peterloes/HRD/Software/Device/EnergyMicro/EFM32G/Include/efm32g200f16.h

/**************************************************************************//**
 * @file
 * @brief CMSIS Cortex-M3 Peripheral Access Layer Header File
 *        for EFM EFM32G200F16
 * @author Energy Micro AS
 * @version 3.20.2
 ******************************************************************************
 * @section License
 * <b>(C) Copyright 2012 Energy Micro AS, http://www.energymicro.com</b>
 ******************************************************************************
 *
 * Permission is granted to anyone to use this software for any purpose,
 * including commercial applications, and to alter it and redistribute it
 * freely, subject to the following restrictions:
 *
 * 1. The origin of this software must not be misrepresented; you must not
 *    claim that you wrote the original software.
 * 2. Altered source versions must be plainly marked as such, and must not be
 *    misrepresented as being the original software.
 * 3. This notice may not be removed or altered from any source distribution.
 *
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
 * Energy Micro AS will not be liable for any consequential, incidental, or
 * special damages, or any other relief, or for any claim by any third party,
 * arising from your use of this Software.
 *
 *****************************************************************************/

#ifndef __EFM32G200F16_H
#define __EFM32G200F16_H

#ifdef __cplusplus
extern "C" {
#endif

/**************************************************************************//**
 * @addtogroup Parts
 * @{
 *****************************************************************************/

/**************************************************************************//**
 * @defgroup EFM32G200F16 EFM32G200F16
 * @{
 *****************************************************************************/

/** Interrupt Number Definition */
typedef enum IRQn
{
/******  Cortex-M3 Processor Exceptions Numbers *******************************************/
  NonMaskableInt_IRQn   = -14,              /*!< 2 Non Maskable Interrupt                 */
  HardFault_IRQn        = -13,              /*!< 3 Cortex-M3 Hard Fault Interrupt         */
  MemoryManagement_IRQn = -12,              /*!< 4 Cortex-M3 Memory Management Interrupt  */
  BusFault_IRQn         = -11,              /*!< 5 Cortex-M3 Bus Fault Interrupt          */
  UsageFault_IRQn       = -10,              /*!< 6 Cortex-M3 Usage Fault Interrupt        */
  SVCall_IRQn           = -5,               /*!< 11 Cortex-M3 SV Call Interrupt           */
  DebugMonitor_IRQn     = -4,               /*!< 12 Cortex-M3 Debug Monitor Interrupt     */
  PendSV_IRQn           = -2,               /*!< 14 Cortex-M3 Pend SV Interrupt           */
  SysTick_IRQn          = -1,               /*!< 15 Cortex-M3 System Tick Interrupt       */

/******  EFM32G Peripheral Interrupt Numbers **********************************************/
  DMA_IRQn              = 0,  /*!< 16+0 EFM32 DMA Interrupt */
  GPIO_EVEN_IRQn        = 1,  /*!< 16+1 EFM32 GPIO_EVEN Interrupt */
  TIMER0_IRQn           = 2,  /*!< 16+2 EFM32 TIMER0 Interrupt */
  USART0_RX_IRQn        = 3,  /*!< 16+3 EFM32 USART0_RX Interrupt */
  USART0_TX_IRQn        = 4,  /*!< 16+4 EFM32 USART0_TX Interrupt */
  ACMP0_IRQn            = 5,  /*!< 16+5 EFM32 ACMP0 Interrupt */
  ADC0_IRQn             = 6,  /*!< 16+6 EFM32 ADC0 Interrupt */
  DAC0_IRQn             = 7,  /*!< 16+7 EFM32 DAC0 Interrupt */
  I2C0_IRQn             = 8,  /*!< 16+8 EFM32 I2C0 Interrupt */
  GPIO_ODD_IRQn         = 9,  /*!< 16+9 EFM32 GPIO_ODD Interrupt */
  TIMER1_IRQn           = 10, /*!< 16+10 EFM32 TIMER1 Interrupt */
  USART1_RX_IRQn        = 12, /*!< 16+12 EFM32 USART1_RX Interrupt */
  USART1_TX_IRQn        = 13, /*!< 16+13 EFM32 USART1_TX Interrupt */
  LEUART0_IRQn          = 18, /*!< 16+18 EFM32 LEUART0 Interrupt */
  LETIMER0_IRQn         = 20, /*!< 16+20 EFM32 LETIMER0 Interrupt */
  PCNT0_IRQn            = 21, /*!< 16+21 EFM32 PCNT0 Interrupt */
  RTC_IRQn              = 24, /*!< 16+24 EFM32 RTC Interrupt */
  CMU_IRQn              = 25, /*!< 16+25 EFM32 CMU Interrupt */
  VCMP_IRQn             = 26, /*!< 16+26 EFM32 VCMP Interrupt */
  MSC_IRQn              = 28, /*!< 16+28 EFM32 MSC Interrupt */
} IRQn_Type;

/**************************************************************************//**
 * @defgroup EFM32G200F16_Core EFM32G200F16 Core
 * @{
 * @brief Processor and Core Peripheral Section
 *****************************************************************************/
#define __MPU_PRESENT             1 /**< Presence of MPU  */
#define __NVIC_PRIO_BITS          3 /**< NVIC interrupt priority bits */
#define __Vendor_SysTickConfig    0 /**< Is 1 if different SysTick counter is used */

/** @} End of group EFM32G200F16_Core */

/**************************************************************************//**
* @defgroup EFM32G200F16_Part EFM32G200F16 Part
* @{
******************************************************************************/

/** Part family */
#define _EFM32_GECKO_FAMILY    1 /**< Gecko EFM32G MCU Family */
#define _EFM_DEVICE              /**< Energy Micro EFM-type microcontroller */

/* If part number is not defined as compiler option, define it */
#if !defined(EFM32G200F16)
#define EFM32G200F16    1 /**< Gecko Part  */
#endif

/** Configure part number */
#define PART_NUMBER          "EFM32G200F16" /**< Part Number */

/** Memory Base addresses and limits */
#define FLASH_MEM_BASE       ((uint32_t) 0x0UL)        /**< FLASH base address  */
#define FLASH_MEM_SIZE       ((uint32_t) 0x10000000UL) /**< FLASH available address space  */
#define FLASH_MEM_END        ((uint32_t) 0xFFFFFFFUL)  /**< FLASH end address  */
#define FLASH_MEM_BITS       ((uint32_t) 0x28UL)       /**< FLASH used bits  */
#define AES_MEM_BASE         ((uint32_t) 0x400E0000UL) /**< AES base address  */
#define AES_MEM_SIZE         ((uint32_t) 0x400UL)      /**< AES available address space  */
#define AES_MEM_END          ((uint32_t) 0x400E03FFUL) /**< AES end address  */
#define AES_MEM_BITS         ((uint32_t) 0x10UL)       /**< AES used bits  */
#define PER_MEM_BASE         ((uint32_t) 0x40000000UL) /**< PER base address  */
#define PER_MEM_SIZE         ((uint32_t) 0xE0000UL)    /**< PER available address space  */
#define PER_MEM_END          ((uint32_t) 0x400DFFFFUL) /**< PER end address  */
#define PER_MEM_BITS         ((uint32_t) 0x20UL)       /**< PER used bits  */
#define RAM_MEM_BASE         ((uint32_t) 0x20000000UL) /**< RAM base address  */
#define RAM_MEM_SIZE         ((uint32_t) 0x8000UL)     /**< RAM available address space  */
#define RAM_MEM_END          ((uint32_t) 0x20007FFFUL) /**< RAM end address  */
#define RAM_MEM_BITS         ((uint32_t) 0x15UL)       /**< RAM used bits  */
#define RAM_CODE_MEM_BASE    ((uint32_t) 0x10000000UL) /**< RAM_CODE base address  */
#define RAM_CODE_MEM_SIZE    ((uint32_t) 0x4000UL)     /**< RAM_CODE available address space  */
#define RAM_CODE_MEM_END     ((uint32_t) 0x10003FFFUL) /**< RAM_CODE end address  */
#define RAM_CODE_MEM_BITS    ((uint32_t) 0x14UL)       /**< RAM_CODE used bits  */
#define EBI_MEM_BASE         ((uint32_t) 0x80000000UL) /**< EBI base address  */
#define EBI_MEM_SIZE         ((uint32_t) 0x10000000UL) /**< EBI available address space  */
#define EBI_MEM_END          ((uint32_t) 0x8FFFFFFFUL) /**< EBI end address  */
#define EBI_MEM_BITS         ((uint32_t) 0x28UL)       /**< EBI used bits  */

/** Bit banding area */
#define BITBAND_PER_BASE     ((uint32_t) 0x42000000UL) /**< Peripheral Address Space bit-band area */
#define BITBAND_RAM_BASE     ((uint32_t) 0x22000000UL) /**< SRAM Address Space bit-band area */

/** Flash and SRAM limits for EFM32G200F16 */
#define FLASH_BASE           (0x00000000UL) /**< Flash Base Address */
#define FLASH_SIZE           (0x00004000UL) /**< Available Flash Memory */
#define FLASH_PAGE_SIZE      512            /**< Flash Memory page size */
#define SRAM_BASE            (0x20000000UL) /**< SRAM Base Address */
#define SRAM_SIZE            (0x00002000UL) /**< Available SRAM Memory */
#define __CM3_REV            0x200          /**< Cortex-M3 Core revision r2p0 */
#define PRS_CHAN_COUNT       8              /**< Number of PRS channels */
#define DMA_CHAN_COUNT       8              /**< Number of DMA channels */

/** AF channels connect the different on-chip peripherals with the af-mux */
#define AFCHAN_MAX           79
#define AFCHANLOC_MAX        4
/** Analog AF channels */
#define AFACHAN_MAX          37

/* Part number capabilities */

#define TIMER_PRESENT         /**< TIMER is available in this part */
#define TIMER_COUNT         2 /**< 2 TIMERs available  */
#define USART_PRESENT         /**< USART is available in this part */
#define USART_COUNT         2 /**< 2 USARTs available  */
#define LEUART_PRESENT        /**< LEUART is available in this part */
#define LEUART_COUNT        1 /**< 1 LEUARTs available  */
#define LETIMER_PRESENT       /**< LETIMER is available in this part */
#define LETIMER_COUNT       1 /**< 1 LETIMERs available  */
#define PCNT_PRESENT          /**< PCNT is available in this part */
#define PCNT_COUNT          1 /**< 1 PCNTs available  */
#define ACMP_PRESENT          /**< ACMP is available in this part */
#define ACMP_COUNT          2 /**< 2 ACMPs available  */
#define DAC_PRESENT           /**< DAC is available in this part */
#define DAC_COUNT           1 /**< 1 DACs available  */
#define ADC_PRESENT           /**< ADC is available in this part */
#define ADC_COUNT           1 /**< 1 ADCs available  */
#define I2C_PRESENT           /**< I2C is available in this part */
#define I2C_COUNT           1 /**< 1 I2Cs available  */
#define DMA_PRESENT
#define DMA_COUNT           1
#define LE_PRESENT
#define LE_COUNT            1
#define MSC_PRESENT
#define MSC_COUNT           1
#define EMU_PRESENT
#define EMU_COUNT           1
#define RMU_PRESENT
#define RMU_COUNT           1
#define CMU_PRESENT
#define CMU_COUNT           1
#define RTC_PRESENT
#define RTC_COUNT           1
#define PRS_PRESENT
#define PRS_COUNT           1
#define GPIO_PRESENT
#define GPIO_COUNT          1
#define VCMP_PRESENT
#define VCMP_COUNT          1
#define HFXTAL_PRESENT
#define HFXTAL_COUNT        1
#define LFXTAL_PRESENT
#define LFXTAL_COUNT        1
#define WDOG_PRESENT
#define WDOG_COUNT          1
#define DBG_PRESENT
#define DBG_COUNT           1
#define BOOTLOADER_PRESENT
#define BOOTLOADER_COUNT    1
#define ANALOG_PRESENT
#define ANALOG_COUNT        1

#include "core_cm3.h"      /* Cortex-M3 processor and core peripherals */
#include "system_efm32g.h" /* System Header */

/** @} End of group EFM32G200F16_Part */

/**************************************************************************//**
 * @defgroup EFM32G200F16_Peripheral_TypeDefs EFM32G200F16 Peripheral TypeDefs
 * @{
 * @brief Device Specific Peripheral Register Structures
 *****************************************************************************/

#include "efm32g_dma_ch.h"

/**************************************************************************//**
 * @defgroup EFM32G200F16_DMA EFM32G200F16 DMA
 * @{
 * @brief EFM32G200F16_DMA Register Declaration
 *****************************************************************************/
typedef struct
{
  __I uint32_t   STATUS;         /**< DMA Status Registers  */
  __O uint32_t   CONFIG;         /**< DMA Configuration Register  */
  __IO uint32_t  CTRLBASE;       /**< Channel Control Data Base Pointer Register  */
  __I uint32_t   ALTCTRLBASE;    /**< Channel Alternate Control Data Base Pointer Register  */
  __I uint32_t   CHWAITSTATUS;   /**< Channel Wait on Request Status Register  */
  __O uint32_t   CHSWREQ;        /**< Channel Software Request Register  */
  __IO uint32_t  CHUSEBURSTS;    /**< Channel Useburst Set Register  */
  __O uint32_t   CHUSEBURSTC;    /**< Channel Useburst Clear Register  */
  __IO uint32_t  CHREQMASKS;     /**< Channel Request Mask Set Register  */
  __O uint32_t   CHREQMASKC;     /**< Channel Request Mask Clear Register  */
  __IO uint32_t  CHENS;          /**< Channel Enable Set Register  */
  __O uint32_t   CHENC;          /**< Channel Enable Clear Register  */
  __IO uint32_t  CHALTS;         /**< Channel Alternate Set Register  */
  __O uint32_t   CHALTC;         /**< Channel Alternate Clear Register  */
  __IO uint32_t  CHPRIS;         /**< Channel Priority Set Register  */
  __O uint32_t   CHPRIC;         /**< Channel Priority Clear Register  */
  uint32_t       RESERVED0[3];   /**< Reserved for future use **/
  __IO uint32_t  ERRORC;         /**< Bus Error Clear Register  */

  uint32_t       RESERVED1[880]; /**< Reserved for future use **/
  __I uint32_t   CHREQSTATUS;    /**< Channel Request Status  */
  uint32_t       RESERVED2[1];   /**< Reserved for future use **/
  __I uint32_t   CHSREQSTATUS;   /**< Channel Single Request Status  */

  uint32_t       RESERVED3[121]; /**< Reserved for future use **/
  __I uint32_t   IF;             /**< Interrupt Flag Register  */
  __IO uint32_t  IFS;            /**< Interrupt Flag Set Register  */
  __IO uint32_t  IFC;            /**< Interrupt Flag Clear Register  */
  __IO uint32_t  IEN;            /**< Interrupt Enable register  */

  uint32_t       RESERVED4[60];  /**< Reserved registers */

  DMA_CH_TypeDef CH[8];          /**< Channel registers */
} DMA_TypeDef;                   /** @} */

#include "efm32g_msc.h"
#include "efm32g_emu.h"
#include "efm32g_rmu.h"

/**************************************************************************//**
 * @defgroup EFM32G200F16_CMU EFM32G200F16 CMU
 * @{
 * @brief EFM32G200F16_CMU Register Declaration
 *****************************************************************************/
typedef struct
{
  __IO uint32_t CTRL;         /**< CMU Control Register  */
  __IO uint32_t HFCORECLKDIV; /**< High Frequency Core Clock Division Register  */
  __IO uint32_t HFPERCLKDIV;  /**< High Frequency Peripheral Clock Division Register  */
  __IO uint32_t HFRCOCTRL;    /**< HFRCO Control Register  */
  __IO uint32_t LFRCOCTRL;    /**< LFRCO Control Register  */
  __IO uint32_t AUXHFRCOCTRL; /**< AUXHFRCO Control Register  */
  __IO uint32_t CALCTRL;      /**< Calibration Control Register  */
  __IO uint32_t CALCNT;       /**< Calibration Counter Register  */
  __IO uint32_t OSCENCMD;     /**< Oscillator Enable/Disable Command Register  */
  __IO uint32_t CMD;          /**< Command Register  */
  __IO uint32_t LFCLKSEL;     /**< Low Frequency Clock Select Register  */
  __I uint32_t  STATUS;       /**< Status Register  */
  __I uint32_t  IF;           /**< Interrupt Flag Register  */
  __IO uint32_t IFS;          /**< Interrupt Flag Set Register  */
  __IO uint32_t IFC;          /**< Interrupt Flag Clear Register  */
  __IO uint32_t IEN;          /**< Interrupt Enable Register  */
  __IO uint32_t HFCORECLKEN0; /**< High Frequency Core Clock Enable Register 0  */
  __IO uint32_t HFPERCLKEN0;  /**< High Frequency Peripheral Clock Enable Register 0  */
  uint32_t      RESERVED0[2]; /**< Reserved for future use **/
  __I uint32_t  SYNCBUSY;     /**< Synchronization Busy Register  */
  __IO uint32_t FREEZE;       /**< Freeze Register  */
  __IO uint32_t LFACLKEN0;    /**< Low Frequency A Clock Enable Register 0  (Async Reg)  */
  uint32_t      RESERVED1[1]; /**< Reserved for future use **/
  __IO uint32_t LFBCLKEN0;    /**< Low Frequency B Clock Enable Register 0 (Async Reg)  */
  uint32_t      RESERVED2[1]; /**< Reserved for future use **/
  __IO uint32_t LFAPRESC0;    /**< Low Frequency A Prescaler Register 0 (Async Reg)  */
  uint32_t      RESERVED3[1]; /**< Reserved for future use **/
  __IO uint32_t LFBPRESC0;    /**< Low Frequency B Prescaler Register 0  (Async Reg)  */
  uint32_t      RESERVED4[1]; /**< Reserved for future use **/
  __IO uint32_t PCNTCTRL;     /**< PCNT Control Register  */

  uint32_t      RESERVED5[1]; /**< Reserved for future use **/
  __IO uint32_t ROUTE;        /**< I/O Routing Register  */
  __IO uint32_t LOCK;         /**< Configuration Lock Register  */
} CMU_TypeDef;                /** @} */

#include "efm32g_timer_cc.h"
#include "efm32g_timer.h"
#include "efm32g_usart.h"
#include "efm32g_leuart.h"
#include "efm32g_rtc.h"
#include "efm32g_letimer.h"
#include "efm32g_pcnt.h"
#include "efm32g_acmp.h"
#include "efm32g_prs_ch.h"

/**************************************************************************//**
 * @defgroup EFM32G200F16_PRS EFM32G200F16 PRS
 * @{
 * @brief EFM32G200F16_PRS Register Declaration
 *****************************************************************************/
typedef struct
{
  __IO uint32_t  SWPULSE;      /**< Software Pulse Register  */
  __IO uint32_t  SWLEVEL;      /**< Software Level Register  */

  uint32_t       RESERVED0[2]; /**< Reserved registers */

  PRS_CH_TypeDef CH[8];        /**< Channel registers */
} PRS_TypeDef;                 /** @} */

#include "efm32g_dac.h"
#include "efm32g_gpio_p.h"
#include "efm32g_gpio.h"
#include "efm32g_vcmp.h"
#include "efm32g_adc.h"
#include "efm32g_i2c.h"
#include "efm32g_wdog.h"
#include "efm32g_dma_descriptor.h"
#include "efm32g_devinfo.h"
#include "efm32g_romtable.h"
#include "efm32g_calibrate.h"

/** @} End of group EFM32G200F16_Peripheral_TypeDefs */

/**************************************************************************//**
 * @defgroup EFM32G200F16_Peripheral_Base EFM32G200F16 Peripheral Memory Map
 * @{
 *****************************************************************************/

#define DMA_BASE          (0x400C2000UL) /**< DMA base address  */
#define MSC_BASE          (0x400C0000UL) /**< MSC base address  */
#define EMU_BASE          (0x400C6000UL) /**< EMU base address  */
#define RMU_BASE          (0x400CA000UL) /**< RMU base address  */
#define CMU_BASE          (0x400C8000UL) /**< CMU base address  */
#define TIMER0_BASE       (0x40010000UL) /**< TIMER0 base address  */
#define TIMER1_BASE       (0x40010400UL) /**< TIMER1 base address  */
#define USART0_BASE       (0x4000C000UL) /**< USART0 base address  */
#define USART1_BASE       (0x4000C400UL) /**< USART1 base address  */
#define LEUART0_BASE      (0x40084000UL) /**< LEUART0 base address  */
#define RTC_BASE          (0x40080000UL) /**< RTC base address  */
#define LETIMER0_BASE     (0x40082000UL) /**< LETIMER0 base address  */
#define PCNT0_BASE        (0x40086000UL) /**< PCNT0 base address  */
#define ACMP0_BASE        (0x40001000UL) /**< ACMP0 base address  */
#define ACMP1_BASE        (0x40001400UL) /**< ACMP1 base address  */
#define PRS_BASE          (0x400CC000UL) /**< PRS base address  */
#define DAC0_BASE         (0x40004000UL) /**< DAC0 base address  */
#define GPIO_BASE         (0x40006000UL) /**< GPIO base address  */
#define VCMP_BASE         (0x40000000UL) /**< VCMP base address  */
#define ADC0_BASE         (0x40002000UL) /**< ADC0 base address  */
#define I2C0_BASE         (0x4000A000UL) /**< I2C0 base address  */
#define WDOG_BASE         (0x40088000UL) /**< WDOG base address  */
#define CALIBRATE_BASE    (0x0FE08000UL) /**< CALIBRATE base address */
#define DEVINFO_BASE      (0x0FE081B0UL) /**< DEVINFO base address */
#define ROMTABLE_BASE     (0xE00FFFD0UL) /**< ROMTABLE base address */
#define LOCKBITS_BASE     (0x0FE04000UL) /**< Lock-bits page base address */
#define USERDATA_BASE     (0x0FE00000UL) /**< User data page base address */

/** @} End of group EFM32G200F16_Peripheral_Base */

/**************************************************************************//**
 * @defgroup EFM32G200F16_Peripheral_Declaration  EFM32G200F16 Peripheral Declarations
 * @{
 *****************************************************************************/

#define DMA          ((DMA_TypeDef *) DMA_BASE)             /**< DMA base pointer */
#define MSC          ((MSC_TypeDef *) MSC_BASE)             /**< MSC base pointer */
#define EMU          ((EMU_TypeDef *) EMU_BASE)             /**< EMU base pointer */
#define RMU          ((RMU_TypeDef *) RMU_BASE)             /**< RMU base pointer */
#define CMU          ((CMU_TypeDef *) CMU_BASE)             /**< CMU base pointer */
#define TIMER0       ((TIMER_TypeDef *) TIMER0_BASE)        /**< TIMER0 base pointer */
#define TIMER1       ((TIMER_TypeDef *) TIMER1_BASE)        /**< TIMER1 base pointer */
#define USART0       ((USART_TypeDef *) USART0_BASE)        /**< USART0 base pointer */
#define USART1       ((USART_TypeDef *) USART1_BASE)        /**< USART1 base pointer */
#define LEUART0      ((LEUART_TypeDef *) LEUART0_BASE)      /**< LEUART0 base pointer */
#define RTC          ((RTC_TypeDef *) RTC_BASE)             /**< RTC base pointer */
#define LETIMER0     ((LETIMER_TypeDef *) LETIMER0_BASE)    /**< LETIMER0 base pointer */
#define PCNT0        ((PCNT_TypeDef *) PCNT0_BASE)          /**< PCNT0 base pointer */
#define ACMP0        ((ACMP_TypeDef *) ACMP0_BASE)          /**< ACMP0 base pointer */
#define ACMP1        ((ACMP_TypeDef *) ACMP1_BASE)          /**< ACMP1 base pointer */
#define PRS          ((PRS_TypeDef *) PRS_BASE)             /**< PRS base pointer */
#define DAC0         ((DAC_TypeDef *) DAC0_BASE)            /**< DAC0 base pointer */
#define GPIO         ((GPIO_TypeDef *) GPIO_BASE)           /**< GPIO base pointer */
#define VCMP         ((VCMP_TypeDef *) VCMP_BASE)           /**< VCMP base pointer */
#define ADC0         ((ADC_TypeDef *) ADC0_BASE)            /**< ADC0 base pointer */
#define I2C0         ((I2C_TypeDef *) I2C0_BASE)            /**< I2C0 base pointer */
#define WDOG         ((WDOG_TypeDef *) WDOG_BASE)           /**< WDOG base pointer */
#define CALIBRATE    ((CALIBRATE_TypeDef *) CALIBRATE_BASE) /**< CALIBRATE base pointer */
#define DEVINFO      ((DEVINFO_TypeDef *) DEVINFO_BASE)     /**< DEVINFO base pointer */
#define ROMTABLE     ((ROMTABLE_TypeDef *) ROMTABLE_BASE)   /**< ROMTABLE base pointer */

/** @} End of group EFM32G200F16_Peripheral_Declaration */

/**************************************************************************//**
 * @defgroup EFM32G200F16_BitFields EFM32G200F16 Bit Fields
 * @{
 *****************************************************************************/

/**************************************************************************//**
 * @addtogroup EFM32G200F16_PRS_Signals
 * @{
 * @brief PRS Signal names
 *****************************************************************************/

#define PRS_VCMP_OUT          ((1 << 16) + 0)  /**< PRS Voltage comparator output */
#define PRS_ACMP0_OUT         ((2 << 16) + 0)  /**< PRS Analog comparator output */
#define PRS_ACMP1_OUT         ((3 << 16) + 0)  /**< PRS Analog comparator output */
#define PRS_DAC0_CH0          ((6 << 16) + 0)  /**< PRS DAC ch0 conversion done */
#define PRS_DAC0_CH1          ((6 << 16) + 1)  /**< PRS DAC ch1 conversion done */
#define PRS_ADC0_SINGLE       ((8 << 16) + 0)  /**< PRS ADC single conversion done */
#define PRS_ADC0_SCAN         ((8 << 16) + 1)  /**< PRS ADC scan conversion done */
#define PRS_USART0_IRTX       ((16 << 16) + 0) /**< PRS USART 0 IRDA out */
#define PRS_USART0_TXC        ((16 << 16) + 1) /**< PRS USART 0 TX complete */
#define PRS_USART0_RXDATAV    ((16 << 16) + 2) /**< PRS USART 0 RX Data Valid */
#define PRS_USART1_IRTX       ((17 << 16) + 0) /**< PRS USART 1 IRDA out */
#define PRS_USART1_TXC        ((17 << 16) + 1) /**< PRS USART 1 TX complete */
#define PRS_USART1_RXDATAV    ((17 << 16) + 2) /**< PRS USART 1 RX Data Valid */
#define PRS_TIMER0_UF         ((28 << 16) + 0) /**< PRS Timer 0 Underflow */
#define PRS_TIMER0_OF         ((28 << 16) + 1) /**< PRS Timer 0 Overflow */
#define PRS_TIMER0_CC0        ((28 << 16) + 2) /**< PRS Timer 0 Compare/Capture 0 */
#define PRS_TIMER0_CC1        ((28 << 16) + 3) /**< PRS Timer 0 Compare/Capture 1 */
#define PRS_TIMER0_CC2        ((28 << 16) + 4) /**< PRS Timer 0 Compare/Capture 2 */
#define PRS_TIMER1_UF         ((29 << 16) + 0) /**< PRS Timer 1 Underflow */
#define PRS_TIMER1_OF         ((29 << 16) + 1) /**< PRS Timer 1 Overflow */
#define PRS_TIMER1_CC0        ((29 << 16) + 2) /**< PRS Timer 1 Compare/Capture 0 */
#define PRS_TIMER1_CC1        ((29 << 16) + 3) /**< PRS Timer 1 Compare/Capture 1 */
#define PRS_TIMER1_CC2        ((29 << 16) + 4) /**< PRS Timer 1 Compare/Capture 2 */
#define PRS_RTC_OF            ((40 << 16) + 0) /**< PRS RTC Overflow */
#define PRS_RTC_COMP0         ((40 << 16) + 1) /**< PRS RTC Compare 0 */
#define PRS_RTC_COMP1         ((40 << 16) + 2) /**< PRS RTC Compare 1 */
#define PRS_GPIO_PIN0         ((48 << 16) + 0) /**< PRS GPIO pin 0 */
#define PRS_GPIO_PIN1         ((48 << 16) + 1) /**< PRS GPIO pin 1 */
#define PRS_GPIO_PIN2         ((48 << 16) + 2) /**< PRS GPIO pin 2 */
#define PRS_GPIO_PIN3         ((48 << 16) + 3) /**< PRS GPIO pin 3 */
#define PRS_GPIO_PIN4         ((48 << 16) + 4) /**< PRS GPIO pin 4 */
#define PRS_GPIO_PIN5         ((48 << 16) + 5) /**< PRS GPIO pin 5 */
#define PRS_GPIO_PIN6         ((48 << 16) + 6) /**< PRS GPIO pin 6 */
#define PRS_GPIO_PIN7         ((48 << 16) + 7) /**< PRS GPIO pin 7 */
#define PRS_GPIO_PIN8         ((49 << 16) + 0) /**< PRS GPIO pin 8 */
#define PRS_GPIO_PIN9         ((49 << 16) + 1) /**< PRS GPIO pin 9 */
#define PRS_GPIO_PIN10        ((49 << 16) + 2) /**< PRS GPIO pin 10 */
#define PRS_GPIO_PIN11        ((49 << 16) + 3) /**< PRS GPIO pin 11 */
#define PRS_GPIO_PIN12        ((49 << 16) + 4) /**< PRS GPIO pin 12 */
#define PRS_GPIO_PIN13        ((49 << 16) + 5) /**< PRS GPIO pin 13 */
#define PRS_GPIO_PIN14        ((49 << 16) + 6) /**< PRS GPIO pin 14 */
#define PRS_GPIO_PIN15        ((49 << 16) + 7) /**< PRS GPIO pin 15 */

/** @} End of group EFM32G200F16_PRS */

#include "efm32g_dmareq.h"
#include "efm32g_dmactrl.h"

/**************************************************************************//**
 * @defgroup EFM32G200F16_DMA_BitFields  EFM32G200F16_DMA Bit Fields
 * @{
 *****************************************************************************/

/* Bit fields for DMA STATUS */
#define _DMA_STATUS_RESETVALUE                          0x10070000UL                          /**< Default value for DMA_STATUS */
#define _DMA_STATUS_MASK                                0x001F00F1UL                          /**< Mask for DMA_STATUS */
#define DMA_STATUS_EN                                   (0x1UL << 0)                          /**< DMA Enable Status */
#define _DMA_STATUS_EN_SHIFT                            0                                     /**< Shift value for DMA_EN */
#define _DMA_STATUS_EN_MASK                             0x1UL                                 /**< Bit mask for DMA_EN */
#define _DMA_STATUS_EN_DEFAULT                          0x00000000UL                          /**< Mode DEFAULT for DMA_STATUS */
#define DMA_STATUS_EN_DEFAULT                           (_DMA_STATUS_EN_DEFAULT << 0)         /**< Shifted mode DEFAULT for DMA_STATUS */
#define _DMA_STATUS_STATE_SHIFT                         4                                     /**< Shift value for DMA_STATE */
#define _DMA_STATUS_STATE_MASK                          0xF0UL                                /**< Bit mask for DMA_STATE */
#define _DMA_STATUS_STATE_DEFAULT                       0x00000000UL                          /**< Mode DEFAULT for DMA_STATUS */
#define _DMA_STATUS_STATE_IDLE                          0x00000000UL                          /**< Mode IDLE for DMA_STATUS */
#define _DMA_STATUS_STATE_RDCHCTRLDATA                  0x00000001UL                          /**< Mode RDCHCTRLDATA for DMA_STATUS */
#define _DMA_STATUS_STATE_RDSRCENDPTR                   0x00000002UL                          /**< Mode RDSRCENDPTR for DMA_STATUS */
#define _DMA_STATUS_STATE_RDDSTENDPTR                   0x00000003UL                          /**< Mode RDDSTENDPTR for DMA_STATUS */
#define _DMA_STATUS_STATE_RDSRCDATA                     0x00000004UL                          /**< Mode RDSRCDATA for DMA_STATUS */
#define _DMA_STATUS_STATE_WRDSTDATA                     0x00000005UL                          /**< Mode WRDSTDATA for DMA_STATUS */
#define _DMA_STATUS_STATE_WAITREQCLR                    0x00000006UL                          /**< Mode WAITREQCLR for DMA_STATUS */
#define _DMA_STATUS_STATE_WRCHCTRLDATA                  0x00000007UL                          /**< Mode WRCHCTRLDATA for DMA_STATUS */
#define _DMA_STATUS_STATE_STALLED                       0x00000008UL                          /**< Mode STALLED for DMA_STATUS */
#define _DMA_STATUS_STATE_DONE                          0x00000009UL                          /**< Mode DONE for DMA_STATUS */
#define _DMA_STATUS_STATE_PERSCATTRANS                  0x0000000AUL                          /**< Mode PERSCATTRANS for DMA_STATUS */
#define DMA_STATUS_STATE_DEFAULT                        (_DMA_STATUS_STATE_DEFAULT << 4)      /**< Shifted mode DEFAULT for DMA_STATUS */
#define DMA_STATUS_STATE_IDLE                           (_DMA_STATUS_STATE_IDLE << 4)         /**< Shifted mode IDLE for DMA_STATUS */
#define DMA_STATUS_STATE_RDCHCTRLDATA                   (_DMA_STATUS_STATE_RDCHCTRLDATA << 4) /**< Shifted mode RDCHCTRLDATA for DMA_STATUS */
#define DMA_STATUS_STATE_RDSRCENDPTR                    (_DMA_STATUS_STATE_RDSRCENDPTR << 4)  /**< Shifted mode RDSRCENDPTR for DMA_STATUS */
#define DMA_STATUS_STATE_RDDSTENDPTR                    (_DMA_STATUS_STATE_RDDSTENDPTR << 4)  /**< Shifted mode RDDSTENDPTR for DMA_STATUS */
#define DMA_STATUS_STATE_RDSRCDATA                      (_DMA_STATUS_STATE_RDSRCDATA << 4)    /**< Shifted mode RDSRCDATA for DMA_STATUS */
#define DMA_STATUS_STATE_WRDSTDATA                      (_DMA_STATUS_STATE_WRDSTDATA << 4)    /**< Shifted mode WRDSTDATA for DMA_STATUS */
#define DMA_STATUS_STATE_WAITREQCLR                     (_DMA_STATUS_STATE_WAITREQCLR << 4)   /**< Shifted mode WAITREQCLR for DMA_STATUS */
#define DMA_STATUS_STATE_WRCHCTRLDATA                   (_DMA_STATUS_STATE_WRCHCTRLDATA << 4) /**< Shifted mode WRCHCTRLDATA for DMA_STATUS */
#define DMA_STATUS_STATE_STALLED                        (_DMA_STATUS_STATE_STALLED << 4)      /**< Shifted mode STALLED for DMA_STATUS */
#define DMA_STATUS_STATE_DONE                           (_DMA_STATUS_STATE_DONE << 4)         /**< Shifted mode DONE for DMA_STATUS */
#define DMA_STATUS_STATE_PERSCATTRANS                   (_DMA_STATUS_STATE_PERSCATTRANS << 4) /**< Shifted mode PERSCATTRANS for DMA_STATUS */
#define _DMA_STATUS_CHNUM_SHIFT                         16                                    /**< Shift value for DMA_CHNUM */
#define _DMA_STATUS_CHNUM_MASK                          0x1F0000UL                            /**< Bit mask for DMA_CHNUM */
#define _DMA_STATUS_CHNUM_DEFAULT                       0x00000007UL                          /**< Mode DEFAULT for DMA_STATUS */
#define DMA_STATUS_CHNUM_DEFAULT                        (_DMA_STATUS_CHNUM_DEFAULT << 16)     /**< Shifted mode DEFAULT for DMA_STATUS */

/* Bit fields for DMA CONFIG */
#define _DMA_CONFIG_RESETVALUE                          0x00000000UL                      /**< Default value for DMA_CONFIG */
#define _DMA_CONFIG_MASK                                0x00000021UL                      /**< Mask for DMA_CONFIG */
#define DMA_CONFIG_EN                                   (0x1UL << 0)                      /**< Enable DMA */
#define _DMA_CONFIG_EN_SHIFT                            0                                 /**< Shift value for DMA_EN */
#define _DMA_CONFIG_EN_MASK                             0x1UL                             /**< Bit mask for DMA_EN */
#define _DMA_CONFIG_EN_DEFAULT                          0x00000000UL                      /**< Mode DEFAULT for DMA_CONFIG */
#define DMA_CONFIG_EN_DEFAULT                           (_DMA_CONFIG_EN_DEFAULT << 0)     /**< Shifted mode DEFAULT for DMA_CONFIG */
#define DMA_CONFIG_CHPROT                               (0x1UL << 5)                      /**< Channel Protection Control */
#define _DMA_CONFIG_CHPROT_SHIFT                        5                                 /**< Shift value for DMA_CHPROT */
#define _DMA_CONFIG_CHPROT_MASK                         0x20UL                            /**< Bit mask for DMA_CHPROT */
#define _DMA_CONFIG_CHPROT_DEFAULT                      0x00000000UL                      /**< Mode DEFAULT for DMA_CONFIG */
#define DMA_CONFIG_CHPROT_DEFAULT                       (_DMA_CONFIG_CHPROT_DEFAULT << 5) /**< Shifted mode DEFAULT for DMA_CONFIG */

/* Bit fields for DMA CTRLBASE */
#define _DMA_CTRLBASE_RESETVALUE                        0x00000000UL                          /**< Default value for DMA_CTRLBASE */
#define _DMA_CTRLBASE_MASK                              0xFFFFFFFFUL                          /**< Mask for DMA_CTRLBASE */
#define _DMA_CTRLBASE_CTRLBASE_SHIFT                    0                                     /**< Shift value for DMA_CTRLBASE */
#define _DMA_CTRLBASE_CTRLBASE_MASK                     0xFFFFFFFFUL                          /**< Bit mask for DMA_CTRLBASE */
#define _DMA_CTRLBASE_CTRLBASE_DEFAULT                  0x00000000UL                          /**< Mode DEFAULT for DMA_CTRLBASE */
#define DMA_CTRLBASE_CTRLBASE_DEFAULT                   (_DMA_CTRLBASE_CTRLBASE_DEFAULT << 0) /**< Shifted mode DEFAULT for DMA_CTRLBASE */

/* Bit fields for DMA ALTCTRLBASE */
#define _DMA_ALTCTRLBASE_RESETVALUE                     0x00000080UL                                /**< Default value for DMA_ALTCTRLBASE */
#define _DMA_ALTCTRLBASE_MASK                           0xFFFFFFFFUL                                /**< Mask for DMA_ALTCTRLBASE */
#define _DMA_ALTCTRLBASE_ALTCTRLBASE_SHIFT              0                                           /**< Shift value for DMA_ALTCTRLBASE */
#define _DMA_ALTCTRLBASE_ALTCTRLBASE_MASK               0xFFFFFFFFUL                                /**< Bit mask for DMA_ALTCTRLBASE */
#define _DMA_ALTCTRLBASE_ALTCTRLBASE_DEFAULT            0x00000080UL                                /**< Mode DEFAULT for DMA_ALTCTRLBASE */
#define DMA_ALTCTRLBASE_ALTCTRLBASE_DEFAULT             (_DMA_ALTCTRLBASE_ALTCTRLBASE_DEFAULT << 0) /**< Shifted mode DEFAULT for DMA_ALTCTRLBASE */

/* Bit fields for DMA CHWAITSTATUS */
#define _DMA_CHWAITSTATUS_RESETVALUE                    0x000000FFUL                                   /**< Default value for DMA_CHWAITSTATUS */
#define _DMA_CHWAITSTATUS_MASK                          0x000000FFUL                                   /**< Mask for DMA_CHWAITSTATUS */
#define DMA_CHWAITSTATUS_CH0WAITSTATUS                  (0x1UL << 0)                                   /**< Channel 0 Wait on Request Status */
#define _DMA_CHWAITSTATUS_CH0WAITSTATUS_SHIFT           0                                              /**< Shift value for DMA_CH0WAITSTATUS */
#define _DMA_CHWAITSTATUS_CH0WAITSTATUS_MASK            0x1UL                                          /**< Bit mask for DMA_CH0WAITSTATUS */
#define _DMA_CHWAITSTATUS_CH0WAITSTATUS_DEFAULT         0x00000001UL                                   /**< Mode DEFAULT for DMA_CHWAITSTATUS */
#define DMA_CHWAITSTATUS_CH0WAITSTATUS_DEFAULT          (_DMA_CHWAITSTATUS_CH0WAITSTATUS_DEFAULT << 0) /**< Shifted mode DEFAULT for DMA_CHWAITSTATUS */
#define DMA_CHWAITSTATUS_CH1WAITSTATUS                  (0x1UL << 1)                                   /**< Channel 1 Wait on Request Status */
#define _DMA_CHWAITSTATUS_CH1WAITSTATUS_SHIFT           1                                              /**< Shift value for DMA_CH1WAITSTATUS */
#define _DMA_CHWAITSTATUS_CH1WAITSTATUS_MASK            0x2UL                                          /**< Bit mask for DMA_CH1WAITSTATUS */
#define _DMA_CHWAITSTATUS_CH1WAITSTATUS_DEFAULT         0x00000001UL                                   /**< Mode DEFAULT for DMA_CHWAITSTATUS */
#define DMA_CHWAITSTATUS_CH1WAITSTATUS_DEFAULT          (_DMA_CHWAITSTATUS_CH1WAITSTATUS_DEFAULT << 1) /**< Shifted mode DEFAULT for DMA_CHWAITSTATUS */
#define DMA_CHWAITSTATUS_CH2WAITSTATUS                  (0x1UL << 2)                                   /**< Channel 2 Wait on Request Status */
#define _DMA_CHWAITSTATUS_CH2WAITSTATUS_SHIFT           2                                              /**< Shift value for DMA_CH2WAITSTATUS */
#define _DMA_CHWAITSTATUS_CH2WAITSTATUS_MASK            0x4UL                                          /**< Bit mask for DMA_CH2WAITSTATUS */
#define _DMA_CHWAITSTATUS_CH2WAITSTATUS_DEFAULT         0x00000001UL                                   /**< Mode DEFAULT for DMA_CHWAITSTATUS */
#define DMA_CHWAITSTATUS_CH2WAITSTATUS_DEFAULT          (_DMA_CHWAITSTATUS_CH2WAITSTATUS_DEFAULT << 2) /**< Shifted mode DEFAULT for DMA_CHWAITSTATUS */
#define DMA_CHWAITSTATUS_CH3WAITSTATUS                  (0x1UL << 3)                                   /**< Channel 3 Wait on Request Status */
#define _DMA_CHWAITSTATUS_CH3WAITSTATUS_SHIFT           3                                              /**< Shift value for DMA_CH3WAITSTATUS */
#define _DMA_CHWAITSTATUS_CH3WAITSTATUS_MASK            0x8UL                                          /**< Bit mask for DMA_CH3WAITSTATUS */
#define _DMA_CHWAITSTATUS_CH3WAITSTATUS_DEFAULT         0x00000001UL                                   /**< Mode DEFAULT for DMA_CHWAITSTATUS */
#define DMA_CHWAITSTATUS_CH3WAITSTATUS_DEFAULT          (_DMA_CHWAITSTATUS_CH3WAITSTATUS_DEFAULT << 3) /**< Shifted mode DEFAULT for DMA_CHWAITSTATUS */
#define DMA_CHWAITSTATUS_CH4WAITSTATUS                  (0x1UL << 4)                                   /**< Channel 4 Wait on Request Status */
#define _DMA_CHWAITSTATUS_CH4WAITSTATUS_SHIFT           4                                              /**< Shift value for DMA_CH4WAITSTATUS */
#define _DMA_CHWAITSTATUS_CH4WAITSTATUS_MASK            0x10UL                                         /**< Bit mask for DMA_CH4WAITSTATUS */
#define _DMA_CHWAITSTATUS_CH4WAITSTATUS_DEFAULT         0x00000001UL                                   /**< Mode DEFAULT for DMA_CHWAITSTATUS */
#define DMA_CHWAITSTATUS_CH4WAITSTATUS_DEFAULT          (_DMA_CHWAITSTATUS_CH4WAITSTATUS_DEFAULT << 4) /**< Shifted mode DEFAULT for DMA_CHWAITSTATUS */
#define DMA_CHWAITSTATUS_CH5WAITSTATUS                  (0x1UL << 5)                                   /**< Channel 5 Wait on Request Status */
#define _DMA_CHWAITSTATUS_CH5WAITSTATUS_SHIFT           5                                              /**< Shift value for DMA_CH5WAITSTATUS */
#define _DMA_CHWAITSTATUS_CH5WAITSTATUS_MASK            0x20UL                                         /**< Bit mask for DMA_CH5WAITSTATUS */
#define _DMA_CHWAITSTATUS_CH5WAITSTATUS_DEFAULT         0x00000001UL                                   /**< Mode DEFAULT for DMA_CHWAITSTATUS */
#define DMA_CHWAITSTATUS_CH5WAITSTATUS_DEFAULT          (_DMA_CHWAITSTATUS_CH5WAITSTATUS_DEFAULT << 5) /**< Shifted mode DEFAULT for DMA_CHWAITSTATUS */
#define DMA_CHWAITSTATUS_CH6WAITSTATUS                  (0x1UL << 6)                                   /**< Channel 6 Wait on Request Status */
#define _DMA_CHWAITSTATUS_CH6WAITSTATUS_SHIFT           6                                              /**< Shift value for DMA_CH6WAITSTATUS */
#define _DMA_CHWAITSTATUS_CH6WAITSTATUS_MASK            0x40UL                                         /**< Bit mask for DMA_CH6WAITSTATUS */
#define _DMA_CHWAITSTATUS_CH6WAITSTATUS_DEFAULT         0x00000001UL                                   /**< Mode DEFAULT for DMA_CHWAITSTATUS */
#define DMA_CHWAITSTATUS_CH6WAITSTATUS_DEFAULT          (_DMA_CHWAITSTATUS_CH6WAITSTATUS_DEFAULT << 6) /**< Shifted mode DEFAULT for DMA_CHWAITSTATUS */
#define DMA_CHWAITSTATUS_CH7WAITSTATUS                  (0x1UL << 7)                                   /**< Channel 7 Wait on Request Status */
#define _DMA_CHWAITSTATUS_CH7WAITSTATUS_SHIFT           7                                              /**< Shift value for DMA_CH7WAITSTATUS */
#define _DMA_CHWAITSTATUS_CH7WAITSTATUS_MASK            0x80UL                                         /**< Bit mask for DMA_CH7WAITSTATUS */
#define _DMA_CHWAITSTATUS_CH7WAITSTATUS_DEFAULT         0x00000001UL                                   /**< Mode DEFAULT for DMA_CHWAITSTATUS */
#define DMA_CHWAITSTATUS_CH7WAITSTATUS_DEFAULT          (_DMA_CHWAITSTATUS_CH7WAITSTATUS_DEFAULT << 7) /**< Shifted mode DEFAULT for DMA_CHWAITSTATUS */

/* Bit fields for DMA CHSWREQ */
#define _DMA_CHSWREQ_RESETVALUE                         0x00000000UL                         /**< Default value for DMA_CHSWREQ */
#define _DMA_CHSWREQ_MASK                               0x000000FFUL                         /**< Mask for DMA_CHSWREQ */
#define DMA_CHSWREQ_CH0SWREQ                            (0x1UL << 0)                         /**< Channel 0 Software Request */
#define _DMA_CHSWREQ_CH0SWREQ_SHIFT                     0                                    /**< Shift value for DMA_CH0SWREQ */
#define _DMA_CHSWREQ_CH0SWREQ_MASK                      0x1UL                                /**< Bit mask for DMA_CH0SWREQ */
#define _DMA_CHSWREQ_CH0SWREQ_DEFAULT                   0x00000000UL                         /**< Mode DEFAULT for DMA_CHSWREQ */
#define DMA_CHSWREQ_CH0SWREQ_DEFAULT                    (_DMA_CHSWREQ_CH0SWREQ_DEFAULT << 0) /**< Shifted mode DEFAULT for DMA_CHSWREQ */
#define DMA_CHSWREQ_CH1SWREQ                            (0x1UL << 1)                         /**< Channel 1 Software Request */
#define _DMA_CHSWREQ_CH1SWREQ_SHIFT                     1                                    /**< Shift value for DMA_CH1SWREQ */
#define _DMA_CHSWREQ_CH1SWREQ_MASK                      0x2UL                                /**< Bit mask for DMA_CH1SWREQ */
#define _DMA_CHSWREQ_CH1SWREQ_DEFAULT                   0x00000000UL                         /**< Mode DEFAULT for DMA_CHSWREQ */
#define DMA_CHSWREQ_CH1SWREQ_DEFAULT                    (_DMA_CHSWREQ_CH1SWREQ_DEFAULT << 1) /**< Shifted mode DEFAULT for DMA_CHSWREQ */
#define DMA_CHSWREQ_CH2SWREQ                            (0x1UL << 2)                         /**< Channel 2 Software Request */
#define _DMA_CHSWREQ_CH2SWREQ_SHIFT                     2                                    /**< Shift value for DMA_CH2SWREQ */
#define _DMA_CHSWREQ_CH2SWREQ_MASK                      0x4UL                                /**< Bit mask for DMA_CH2SWREQ */
#define _DMA_CHSWREQ_CH2SWREQ_DEFAULT                   0x00000000UL                         /**< Mode DEFAULT for DMA_CHSWREQ */
#define DMA_CHSWREQ_CH2SWREQ_DEFAULT                    (_DMA_CHSWREQ_CH2SWREQ_DEFAULT << 2) /**< Shifted mode DEFAULT for DMA_CHSWREQ */
#define DMA_CHSWREQ_CH3SWREQ                            (0x1UL << 3)                         /**< Channel 3 Software Request */
#define _DMA_CHSWREQ_CH3SWREQ_SHIFT                     3                                    /**< Shift value for DMA_CH3SWREQ */
#define _DMA_CHSWREQ_CH3SWREQ_MASK                      0x8UL                                /**< Bit mask for DMA_CH3SWREQ */
#define _DMA_CHSWREQ_CH3SWREQ_DEFAULT                   0x00000000UL                         /**< Mode DEFAULT for DMA_CHSWREQ */
#define DMA_CHSWREQ_CH3SWREQ_DEFAULT                    (_DMA_CHSWREQ_CH3SWREQ_DEFAULT << 3) /**< Shifted mode DEFAULT for DMA_CHSWREQ */
#define DMA_CHSWREQ_CH4SWREQ                            (0x1UL << 4)                         /**< Channel 4 Software Request */
#define _DMA_CHSWREQ_CH4SWREQ_SHIFT                     4                                    /**< Shift value for DMA_CH4SWREQ */
#define _DMA_CHSWREQ_CH4SWREQ_MASK                      0x10UL                               /**< Bit mask for DMA_CH4SWREQ */
#define _DMA_CHSWREQ_CH4SWREQ_DEFAULT                   0x00000000UL                         /**< Mode DEFAULT for DMA_CHSWREQ */
#define DMA_CHSWREQ_CH4SWREQ_DEFAULT                    (_DMA_CHSWREQ_CH4SWREQ_DEFAULT << 4) /**< Shifted mode DEFAULT for DMA_CHSWREQ */
#define DMA_CHSWREQ_CH5SWREQ                            (0x1UL << 5)                         /**< Channel 5 Software Request */
#define _DMA_CHSWREQ_CH5SWREQ_SHIFT                     5                                    /**< Shift value for DMA_CH5SWREQ */
#define _DMA_CHSWREQ_CH5SWREQ_MASK                      0x20UL                               /**< Bit mask for DMA_CH5SWREQ */
#define _DMA_CHSWREQ_CH5SWREQ_DEFAULT                   0x00000000UL                         /**< Mode DEFAULT for DMA_CHSWREQ */
#define DMA_CHSWREQ_CH5SWREQ_DEFAULT                    (_DMA_CHSWREQ_CH5SWREQ_DEFAULT << 5) /**< Shifted mode DEFAULT for DMA_CHSWREQ */
#define DMA_CHSWREQ_CH6SWREQ                            (0x1UL << 6)                         /**< Channel 6 Software Request */
#define _DMA_CHSWREQ_CH6SWREQ_SHIFT                     6                                    /**< Shift value for DMA_CH6SWREQ */
#define _DMA_CHSWREQ_CH6SWREQ_MASK                      0x40UL                               /**< Bit mask for DMA_CH6SWREQ */
#define _DMA_CHSWREQ_CH6SWREQ_DEFAULT                   0x00000000UL                         /**< Mode DEFAULT for DMA_CHSWREQ */
#define DMA_CHSWREQ_CH6SWREQ_DEFAULT                    (_DMA_CHSWREQ_CH6SWREQ_DEFAULT << 6) /**< Shifted mode DEFAULT for DMA_CHSWREQ */
#define DMA_CHSWREQ_CH7SWREQ                            (0x1UL << 7)                         /**< Channel 7 Software Request */
#define _DMA_CHSWREQ_CH7SWREQ_SHIFT                     7                                    /**< Shift value for DMA_CH7SWREQ */
#define _DMA_CHSWREQ_CH7SWREQ_MASK                      0x80UL                               /**< Bit mask for DMA_CH7SWREQ */
#define _DMA_CHSWREQ_CH7SWREQ_DEFAULT                   0x00000000UL                         /**< Mode DEFAULT for DMA_CHSWREQ */
#define DMA_CHSWREQ_CH7SWREQ_DEFAULT                    (_DMA_CHSWREQ_CH7SWREQ_DEFAULT << 7) /**< Shifted mode DEFAULT for DMA_CHSWREQ */

/* Bit fields for DMA CHUSEBURSTS */
#define _DMA_CHUSEBURSTS_RESETVALUE                     0x00000000UL                                        /**< Default value for DMA_CHUSEBURSTS */
#define _DMA_CHUSEBURSTS_MASK                           0x000000FFUL                                        /**< Mask for DMA_CHUSEBURSTS */
#define DMA_CHUSEBURSTS_CH0USEBURSTS                    (0x1UL << 0)                                        /**< Channel 0 Useburst Set */
#define _DMA_CHUSEBURSTS_CH0USEBURSTS_SHIFT             0                                                   /**< Shift value for DMA_CH0USEBURSTS */
#define _DMA_CHUSEBURSTS_CH0USEBURSTS_MASK              0x1UL                                               /**< Bit mask for DMA_CH0USEBURSTS */
#define _DMA_CHUSEBURSTS_CH0USEBURSTS_DEFAULT           0x00000000UL                                        /**< Mode DEFAULT for DMA_CHUSEBURSTS */
#define _DMA_CHUSEBURSTS_CH0USEBURSTS_SINGLEANDBURST    0x00000000UL                                        /**< Mode SINGLEANDBURST for DMA_CHUSEBURSTS */
#define _DMA_CHUSEBURSTS_CH0USEBURSTS_BURSTONLY         0x00000001UL                                        /**< Mode BURSTONLY for DMA_CHUSEBURSTS */
#define DMA_CHUSEBURSTS_CH0USEBURSTS_DEFAULT            (_DMA_CHUSEBURSTS_CH0USEBURSTS_DEFAULT << 0)        /**< Shifted mode DEFAULT for DMA_CHUSEBURSTS */
#define DMA_CHUSEBURSTS_CH0USEBURSTS_SINGLEANDBURST     (_DMA_CHUSEBURSTS_CH0USEBURSTS_SINGLEANDBURST << 0) /**< Shifted mode SINGLEANDBURST for DMA_CHUSEBURSTS */
#define DMA_CHUSEBURSTS_CH0USEBURSTS_BURSTONLY          (_DMA_CHUSEBURSTS_CH0USEBURSTS_BURSTONLY << 0)      /**< Shifted mode BURSTONLY for DMA_CHUSEBURSTS */
#define DMA_CHUSEBURSTS_CH1USEBURSTS                    (0x1UL << 1)                                        /**< Channel 1 Useburst Set */
#define _DMA_CHUSEBURSTS_CH1USEBURSTS_SHIFT             1                                                   /**< Shift value for DMA_CH1USEBURSTS */
#define _DMA_CHUSEBURSTS_CH1USEBURSTS_MASK              0x2UL                                               /**< Bit mask for DMA_CH1USEBURSTS */
#define _DMA_CHUSEBURSTS_CH1USEBURSTS_DEFAULT           0x00000000UL                                        /**< Mode DEFAULT for DMA_CHUSEBURSTS */
#define DMA_CHUSEBURSTS_CH1USEBURSTS_DEFAULT            (_DMA_CHUSEBURSTS_CH1USEBURSTS_DEFAULT << 1)        /**< Shifted mode DEFAULT for DMA_CHUSEBURSTS */
#define DMA_CHUSEBURSTS_CH2USEBURSTS                    (0x1UL << 2)                                        /**< Channel 2 Useburst Set */
#define _DMA_CHUSEBURSTS_CH2USEBURSTS_SHIFT             2                                                   /**< Shift value for DMA_CH2USEBURSTS */
#define _DMA_CHUSEBURSTS_CH2USEBURSTS_MASK              0x4UL                                               /**< Bit mask for DMA_CH2USEBURSTS */
#define _DMA_CHUSEBURSTS_CH2USEBURSTS_DEFAULT           0x00000000UL                                        /**< Mode DEFAULT for DMA_CHUSEBURSTS */
#define DMA_CHUSEBURSTS_CH2USEBURSTS_DEFAULT            (_DMA_CHUSEBURSTS_CH2USEBURSTS_DEFAULT << 2)        /**< Shifted mode DEFAULT for DMA_CHUSEBURSTS */
#define DMA_CHUSEBURSTS_CH3USEBURSTS                    (0x1UL << 3)                                        /**< Channel 3 Useburst Set */
#define _DMA_CHUSEBURSTS_CH3USEBURSTS_SHIFT             3                                                   /**< Shift value for DMA_CH3USEBURSTS */
#define _DMA_CHUSEBURSTS_CH3USEBURSTS_MASK              0x8UL                                               /**< Bit mask for DMA_CH3USEBURSTS */
#define _DMA_CHUSEBURSTS_CH3USEBURSTS_DEFAULT           0x00000000UL                                        /**< Mode DEFAULT for DMA_CHUSEBURSTS */
#define DMA_CHUSEBURSTS_CH3USEBURSTS_DEFAULT            (_DMA_CHUSEBURSTS_CH3USEBURSTS_DEFAULT << 3)        /**< Shifted mode DEFAULT for DMA_CHUSEBURSTS */
#define DMA_CHUSEBURSTS_CH4USEBURSTS                    (0x1UL << 4)                                        /**< Channel 4 Useburst Set */
#define _DMA_CHUSEBURSTS_CH4USEBURSTS_SHIFT             4                                                   /**< Shift value for DMA_CH4USEBURSTS */
#define _DMA_CHUSEBURSTS_CH4USEBURSTS_MASK              0x10UL                                              /**< Bit mask for DMA_CH4USEBURSTS */
#define _DMA_CHUSEBURSTS_CH4USEBURSTS_DEFAULT           0x00000000UL                                        /**< Mode DEFAULT for DMA_CHUSEBURSTS */
#define DMA_CHUSEBURSTS_CH4USEBURSTS_DEFAULT            (_DMA_CHUSEBURSTS_CH4USEBURSTS_DEFAULT << 4)        /**< Shifted mode DEFAULT for DMA_CHUSEBURSTS */
#define DMA_CHUSEBURSTS_CH5USEBURSTS                    (0x1UL << 5)                                        /**< Channel 5 Useburst Set */
#define _DMA_CHUSEBURSTS_CH5USEBURSTS_SHIFT             5                                                   /**< Shift value for DMA_CH5USEBURSTS */
#define _DMA_CHUSEBURSTS_CH5USEBURSTS_MASK              0x20UL                                              /**< Bit mask for DMA_CH5USEBURSTS */
#define _DMA_CHUSEBURSTS_CH5USEBURSTS_DEFAULT           0x00000000UL                                        /**< Mode DEFAULT for DMA_CHUSEBURSTS */
#define DMA_CHUSEBURSTS_CH5USEBURSTS_DEFAULT            (_DMA_CHUSEBURSTS_CH5USEBURSTS_DEFAULT << 5)        /**< Shifted mode DEFAULT for DMA_CHUSEBURSTS */
#define DMA_CHUSEBURSTS_CH6USEBURSTS                    (0x1UL << 6)                                        /**< Channel 6 Useburst Set */
#define _DMA_CHUSEBURSTS_CH6USEBURSTS_SHIFT             6                                                   /**< Shift value for DMA_CH6USEBURSTS */
#define _DMA_CHUSEBURSTS_CH6USEBURSTS_MASK              0x40UL                                              /**< Bit mask for DMA_CH6USEBURSTS */
#define _DMA_CHUSEBURSTS_CH6USEBURSTS_DEFAULT           0x00000000UL                                        /**< Mode DEFAULT for DMA_CHUSEBURSTS */
#define DMA_CHUSEBURSTS_CH6USEBURSTS_DEFAULT            (_DMA_CHUSEBURSTS_CH6USEBURSTS_DEFAULT << 6)        /**< Shifted mode DEFAULT for DMA_CHUSEBURSTS */
#define DMA_CHUSEBURSTS_CH7USEBURSTS                    (0x1UL << 7)                                        /**< Channel 7 Useburst Set */
#define _DMA_CHUSEBURSTS_CH7USEBURSTS_SHIFT             7                                                   /**< Shift value for DMA_CH7USEBURSTS */
#define _DMA_CHUSEBURSTS_CH7USEBURSTS_MASK              0x80UL                                              /**< Bit mask for DMA_CH7USEBURSTS */
#define _DMA_CHUSEBURSTS_CH7USEBURSTS_DEFAULT           0x00000000UL                                        /**< Mode DEFAULT for DMA_CHUSEBURSTS */
#define DMA_CHUSEBURSTS_CH7USEBURSTS_DEFAULT            (_DMA_CHUSEBURSTS_CH7USEBURSTS_DEFAULT << 7)        /**< Shifted mode DEFAULT for DMA_CHUSEBURSTS */

/* Bit fields for DMA CHUSEBURSTC */
#define _DMA_CHUSEBURSTC_RESETVALUE                     0x00000000UL                                 /**< Default value for DMA_CHUSEBURSTC */
#define _DMA_CHUSEBURSTC_MASK                           0x000000FFUL                                 /**< Mask for DMA_CHUSEBURSTC */
#define DMA_CHUSEBURSTC_CH0USEBURSTC                    (0x1UL << 0)                                 /**< Channel 0 Useburst Clear */
#define _DMA_CHUSEBURSTC_CH0USEBURSTC_SHIFT             0                                            /**< Shift value for DMA_CH0USEBURSTC */
#define _DMA_CHUSEBURSTC_CH0USEBURSTC_MASK              0x1UL                                        /**< Bit mask for DMA_CH0USEBURSTC */
#define _DMA_CHUSEBURSTC_CH0USEBURSTC_DEFAULT           0x00000000UL                                 /**< Mode DEFAULT for DMA_CHUSEBURSTC */
#define DMA_CHUSEBURSTC_CH0USEBURSTC_DEFAULT            (_DMA_CHUSEBURSTC_CH0USEBURSTC_DEFAULT << 0) /**< Shifted mode DEFAULT for DMA_CHUSEBURSTC */
#define DMA_CHUSEBURSTC_CH1USEBURSTC                    (0x1UL << 1)                                 /**< Channel 1 Useburst Clear */
#define _DMA_CHUSEBURSTC_CH1USEBURSTC_SHIFT             1                                            /**< Shift value for DMA_CH1USEBURSTC */
#define _DMA_CHUSEBURSTC_CH1USEBURSTC_MASK              0x2UL                                        /**< Bit mask for DMA_CH1USEBURSTC */
#define _DMA_CHUSEBURSTC_CH1USEBURSTC_DEFAULT           0x00000000UL                                 /**< Mode DEFAULT for DMA_CHUSEBURSTC */
#define DMA_CHUSEBURSTC_CH1USEBURSTC_DEFAULT            (_DMA_CHUSEBURSTC_CH1USEBURSTC_DEFAULT << 1) /**< Shifted mode DEFAULT for DMA_CHUSEBURSTC */
#define DMA_CHUSEBURSTC_CH2USEBURSTC                    (0x1UL << 2)                                 /**< Channel 2 Useburst Clear */
#define _DMA_CHUSEBURSTC_CH2USEBURSTC_SHIFT             2                                            /**< Shift value for DMA_CH2USEBURSTC */
#define _DMA_CHUSEBURSTC_CH2USEBURSTC_MASK              0x4UL                                        /**< Bit mask for DMA_CH2USEBURSTC */
#define _DMA_CHUSEBURSTC_CH2USEBURSTC_DEFAULT           0x00000000UL                                 /**< Mode DEFAULT for DMA_CHUSEBURSTC */
#define DMA_CHUSEBURSTC_CH2USEBURSTC_DEFAULT            (_DMA_CHUSEBURSTC_CH2USEBURSTC_DEFAULT << 2) /**< Shifted mode DEFAULT for DMA_CHUSEBURSTC */
#define DMA_CHUSEBURSTC_CH3USEBURSTC                    (0x1UL << 3)                                 /**< Channel 3 Useburst Clear */
#define _DMA_CHUSEBURSTC_CH3USEBURSTC_SHIFT             3                                            /**< Shift value for DMA_CH3USEBURSTC */
#define _DMA_CHUSEBURSTC_CH3USEBURSTC_MASK              0x8UL                                        /**< Bit mask for DMA_CH3USEBURSTC */
#define _DMA_CHUSEBURSTC_CH3USEBURSTC_DEFAULT           0x00000000UL                                 /**< Mode DEFAULT for DMA_CHUSEBURSTC */
#define DMA_CHUSEBURSTC_CH3USEBURSTC_DEFAULT            (_DMA_CHUSEBURSTC_CH3USEBURSTC_DEFAULT << 3) /**< Shifted mode DEFAULT for DMA_CHUSEBURSTC */
#define DMA_CHUSEBURSTC_CH4USEBURSTC                    (0x1UL << 4)                                 /**< Channel 4 Useburst Clear */
#define _DMA_CHUSEBURSTC_CH4USEBURSTC_SHIFT             4                                            /**< Shift value for DMA_CH4USEBURSTC */
#define _DMA_CHUSEBURSTC_CH4USEBURSTC_MASK              0x10UL                                       /**< Bit mask for DMA_CH4USEBURSTC */
#define _DMA_CHUSEBURSTC_CH4USEBURSTC_DEFAULT           0x00000000UL                                 /**< Mode DEFAULT for DMA_CHUSEBURSTC */
#define DMA_CHUSEBURSTC_CH4USEBURSTC_DEFAULT            (_DMA_CHUSEBURSTC_CH4USEBURSTC_DEFAULT << 4) /**< Shifted mode DEFAULT for DMA_CHUSEBURSTC */
#define DMA_CHUSEBURSTC_CH5USEBURSTC                    (0x1UL << 5)                                 /**< Channel 5 Useburst Clear */
#define _DMA_CHUSEBURSTC_CH5USEBURSTC_SHIFT             5                                            /**< Shift value for DMA_CH5USEBURSTC */
#define _DMA_CHUSEBURSTC_CH5USEBURSTC_MASK              0x20UL                                       /**< Bit mask for DMA_CH5USEBURSTC */
#define _DMA_CHUSEBURSTC_CH5USEBURSTC_DEFAULT           0x00000000UL                                 /**< Mode DEFAULT for DMA_CHUSEBURSTC */
#define DMA_CHUSEBURSTC_CH5USEBURSTC_DEFAULT            (_DMA_CHUSEBURSTC_CH5USEBURSTC_DEFAULT << 5) /**< Shifted mode DEFAULT for DMA_CHUSEBURSTC */
#define DMA_CHUSEBURSTC_CH6USEBURSTC                    (0x1UL << 6)                                 /**< Channel 6 Useburst Clear */
#define _DMA_CHUSEBURSTC_CH6USEBURSTC_SHIFT             6                                            /**< Shift value for DMA_CH6USEBURSTC */
#define _DMA_CHUSEBURSTC_CH6USEBURSTC_MASK              0x40UL                                       /**< Bit mask for DMA_CH6USEBURSTC */
#define _DMA_CHUSEBURSTC_CH6USEBURSTC_DEFAULT           0x00000000UL                                 /**< Mode DEFAULT for DMA_CHUSEBURSTC */
#define DMA_CHUSEBURSTC_CH6USEBURSTC_DEFAULT            (_DMA_CHUSEBURSTC_CH6USEBURSTC_DEFAULT << 6) /**< Shifted mode DEFAULT for DMA_CHUSEBURSTC */
#define DMA_CHUSEBURSTC_CH7USEBURSTC                    (0x1UL << 7)                                 /**< Channel 7 Useburst Clear */
#define _DMA_CHUSEBURSTC_CH7USEBURSTC_SHIFT             7                                            /**< Shift value for DMA_CH7USEBURSTC */
#define _DMA_CHUSEBURSTC_CH7USEBURSTC_MASK              0x80UL                                       /**< Bit mask for DMA_CH7USEBURSTC */
#define _DMA_CHUSEBURSTC_CH7USEBURSTC_DEFAULT           0x00000000UL                                 /**< Mode DEFAULT for DMA_CHUSEBURSTC */
#define DMA_CHUSEBURSTC_CH7USEBURSTC_DEFAULT            (_DMA_CHUSEBURSTC_CH7USEBURSTC_DEFAULT << 7) /**< Shifted mode DEFAULT for DMA_CHUSEBURSTC */

/* Bit fields for DMA CHREQMASKS */
#define _DMA_CHREQMASKS_RESETVALUE                      0x00000000UL                               /**< Default value for DMA_CHREQMASKS */
#define _DMA_CHREQMASKS_MASK                            0x000000FFUL                               /**< Mask for DMA_CHREQMASKS */
#define DMA_CHREQMASKS_CH0REQMASKS                      (0x1UL << 0)                               /**< Channel 0 Request Mask Set */
#define _DMA_CHREQMASKS_CH0REQMASKS_SHIFT               0                                          /**< Shift value for DMA_CH0REQMASKS */
#define _DMA_CHREQMASKS_CH0REQMASKS_MASK                0x1UL                                      /**< Bit mask for DMA_CH0REQMASKS */
#define _DMA_CHREQMASKS_CH0REQMASKS_DEFAULT             0x00000000UL                               /**< Mode DEFAULT for DMA_CHREQMASKS */
#define DMA_CHREQMASKS_CH0REQMASKS_DEFAULT              (_DMA_CHREQMASKS_CH0REQMASKS_DEFAULT << 0) /**< Shifted mode DEFAULT for DMA_CHREQMASKS */
#define DMA_CHREQMASKS_CH1REQMASKS                      (0x1UL << 1)                               /**< Channel 1 Request Mask Set */
#define _DMA_CHREQMASKS_CH1REQMASKS_SHIFT               1                                          /**< Shift value for DMA_CH1REQMASKS */
#define _DMA_CHREQMASKS_CH1REQMASKS_MASK                0x2UL                                      /**< Bit mask for DMA_CH1REQMASKS */
#define _DMA_CHREQMASKS_CH1REQMASKS_DEFAULT             0x00000000UL                               /**< Mode DEFAULT for DMA_CHREQMASKS */
#define DMA_CHREQMASKS_CH1REQMASKS_DEFAULT              (_DMA_CHREQMASKS_CH1REQMASKS_DEFAULT << 1) /**< Shifted mode DEFAULT for DMA_CHREQMASKS */
#define DMA_CHREQMASKS_CH2REQMASKS                      (0x1UL << 2)                               /**< Channel 2 Request Mask Set */
#define _DMA_CHREQMASKS_CH2REQMASKS_SHIFT               2                                          /**< Shift value for DMA_CH2REQMASKS */
#define _DMA_CHREQMASKS_CH2REQMASKS_MASK                0x4UL                                      /**< Bit mask for DMA_CH2REQMASKS */
#define _DMA_CHREQMASKS_CH2REQMASKS_DEFAULT             0x00000000UL                               /**< Mode DEFAULT for DMA_CHREQMASKS */
#define DMA_CHREQMASKS_CH2REQMASKS_DEFAULT              (_DMA_CHREQMASKS_CH2REQMASKS_DEFAULT << 2) /**< Shifted mode DEFAULT for DMA_CHREQMASKS */
#define DMA_CHREQMASKS_CH3REQMASKS                      (0x1UL << 3)                               /**< Channel 3 Request Mask Set */
#define _DMA_CHREQMASKS_CH3REQMASKS_SHIFT               3                                          /**< Shift value for DMA_CH3REQMASKS */
#define _DMA_CHREQMASKS_CH3REQMASKS_MASK                0x8UL                                      /**< Bit mask for DMA_CH3REQMASKS */
#define _DMA_CHREQMASKS_CH3REQMASKS_DEFAULT             0x00000000UL                               /**< Mode DEFAULT for DMA_CHREQMASKS */
#define DMA_CHREQMASKS_CH3REQMASKS_DEFAULT              (_DMA_CHREQMASKS_CH3REQMASKS_DEFAULT << 3) /**< Shifted mode DEFAULT for DMA_CHREQMASKS */
#define DMA_CHREQMASKS_CH4REQMASKS                      (0x1UL << 4)                               /**< Channel 4 Request Mask Set */
#define _DMA_CHREQMASKS_CH4REQMASKS_SHIFT               4                                          /**< Shift value for DMA_CH4REQMASKS */
#define _DMA_CHREQMASKS_CH4REQMASKS_MASK                0x10UL                                     /**< Bit mask for DMA_CH4REQMASKS */
#define _DMA_CHREQMASKS_CH4REQMASKS_DEFAULT             0x00000000UL                               /**< Mode DEFAULT for DMA_CHREQMASKS */
#define DMA_CHREQMASKS_CH4REQMASKS_DEFAULT              (_DMA_CHREQMASKS_CH4REQMASKS_DEFAULT << 4) /**< Shifted mode DEFAULT for DMA_CHREQMASKS */
#define DMA_CHREQMASKS_CH5REQMASKS                      (0x1UL << 5)                               /**< Channel 5 Request Mask Set */
#define _DMA_CHREQMASKS_CH5REQMASKS_SHIFT               5                                          /**< Shift value for DMA_CH5REQMASKS */
#define _DMA_CHREQMASKS_CH5REQMASKS_MASK                0x20UL                                     /**< Bit mask for DMA_CH5REQMASKS */
#define _DMA_CHREQMASKS_CH5REQMASKS_DEFAULT             0x00000000UL                               /**< Mode DEFAULT for DMA_CHREQMASKS */
#define DMA_CHREQMASKS_CH5REQMASKS_DEFAULT              (_DMA_CHREQMASKS_CH5REQMASKS_DEFAULT << 5) /**< Shifted mode DEFAULT for DMA_CHREQMASKS */
#define DMA_CHREQMASKS_CH6REQMASKS                      (0x1UL << 6)                               /**< Channel 6 Request Mask Set */
#define _DMA_CHREQMASKS_CH6REQMASKS_SHIFT               6                                          /**< Shift value for DMA_CH6REQMASKS */
#define _DMA_CHREQMASKS_CH6REQMASKS_MASK                0x40UL                                     /**< Bit mask for DMA_CH6REQMASKS */
#define _DMA_CHREQMASKS_CH6REQMASKS_DEFAULT             0x00000000UL                               /**< Mode DEFAULT for DMA_CHREQMASKS */
#define DMA_CHREQMASKS_CH6REQMASKS_DEFAULT              (_DMA_CHREQMASKS_CH6REQMASKS_DEFAULT << 6) /**< Shifted mode DEFAULT for DMA_CHREQMASKS */
#define DMA_CHREQMASKS_CH7REQMASKS                      (0x1UL << 7)                               /**< Channel 7 Request Mask Set */
#define _DMA_CHREQMASKS_CH7REQMASKS_SHIFT               7                                          /**< Shift value for DMA_CH7REQMASKS */
#define _DMA_CHREQMASKS_CH7REQMASKS_MASK                0x80UL                                     /**< Bit mask for DMA_CH7REQMASKS */
#define _DMA_CHREQMASKS_CH7REQMASKS_DEFAULT             0x00000000UL                               /**< Mode DEFAULT for DMA_CHREQMASKS */
#define DMA_CHREQMASKS_CH7REQMASKS_DEFAULT              (_DMA_CHREQMASKS_CH7REQMASKS_DEFAULT << 7) /**< Shifted mode DEFAULT for DMA_CHREQMASKS */

/* Bit fields for DMA CHREQMASKC */
#define _DMA_CHREQMASKC_RESETVALUE                      0x00000000UL                               /**< Default value for DMA_CHREQMASKC */
#define _DMA_CHREQMASKC_MASK                            0x000000FFUL                               /**< Mask for DMA_CHREQMASKC */
#define DMA_CHREQMASKC_CH0REQMASKC                      (0x1UL << 0)                               /**< Channel 0 Request Mask Clear */
#define _DMA_CHREQMASKC_CH0REQMASKC_SHIFT               0                                          /**< Shift value for DMA_CH0REQMASKC */
#define _DMA_CHREQMASKC_CH0REQMASKC_MASK                0x1UL                                      /**< Bit mask for DMA_CH0REQMASKC */
#define _DMA_CHREQMASKC_CH0REQMASKC_DEFAULT             0x00000000UL                               /**< Mode DEFAULT for DMA_CHREQMASKC */
#define DMA_CHREQMASKC_CH0REQMASKC_DEFAULT              (_DMA_CHREQMASKC_CH0REQMASKC_DEFAULT << 0) /**< Shifted mode DEFAULT for DMA_CHREQMASKC */
#define DMA_CHREQMASKC_CH1REQMASKC                      (0x1UL << 1)                               /**< Channel 1 Request Mask Clear */
#define _DMA_CHREQMASKC_CH1REQMASKC_SHIFT               1                                          /**< Shift value for DMA_CH1REQMASKC */
#define _DMA_CHREQMASKC_CH1REQMASKC_MASK                0x2UL                                      /**< Bit mask for DMA_CH1REQMASKC */
#define _DMA_CHREQMASKC_CH1REQMASKC_DEFAULT             0x00000000UL                               /**< Mode DEFAULT for DMA_CHREQMASKC */
#define DMA_CHREQMASKC_CH1REQMASKC_DEFAULT              (_DMA_CHREQMASKC_CH1REQMASKC_DEFAULT << 1) /**< Shifted mode DEFAULT for DMA_CHREQMASKC */
#define DMA_CHREQMASKC_CH2REQMASKC                      (0x1UL << 2)                               /**< Channel 2 Request Mask Clear */
#define _DMA_CHREQMASKC_CH2REQMASKC_SHIFT               2                                          /**< Shift value for DMA_CH2REQMASKC */
#define _DMA_CHREQMASKC_CH2REQMASKC_MASK                0x4UL                                      /**< Bit mask for DMA_CH2REQMASKC */
#define _DMA_CHREQMASKC_CH2REQMASKC_DEFAULT             0x00000000UL                               /**< Mode DEFAULT for DMA_CHREQMASKC */
#define DMA_CHREQMASKC_CH2REQMASKC_DEFAULT              (_DMA_CHREQMASKC_CH2REQMASKC_DEFAULT << 2) /**< Shifted mode DEFAULT for DMA_CHREQMASKC */
#define DMA_CHREQMASKC_CH3REQMASKC                      (0x1UL << 3)                               /**< Channel 3 Request Mask Clear */
#define _DMA_CHREQMASKC_CH3REQMASKC_SHIFT               3                                          /**< Shift value for DMA_CH3REQMASKC */
#define _DMA_CHREQMASKC_CH3REQMASKC_MASK                0x8UL                                      /**< Bit mask for DMA_CH3REQMASKC */
#define _DMA_CHREQMASKC_CH3REQMASKC_DEFAULT             0x00000000UL                               /**< Mode DEFAULT for DMA_CHREQMASKC */
#define DMA_CHREQMASKC_CH3REQMASKC_DEFAULT              (_DMA_CHREQMASKC_CH3REQMASKC_DEFAULT << 3) /**< Shifted mode DEFAULT for DMA_CHREQMASKC */
#define DMA_CHREQMASKC_CH4REQMASKC                      (0x1UL << 4)                               /**< Channel 4 Request Mask Clear */
#define _DMA_CHREQMASKC_CH4REQMASKC_SHIFT               4                                          /**< Shift value for DMA_CH4REQMASKC */
#define _DMA_CHREQMASKC_CH4REQMASKC_MASK                0x10UL                                     /**< Bit mask for DMA_CH4REQMASKC */
#define _DMA_CHREQMASKC_CH4REQMASKC_DEFAULT             0x00000000UL                               /**< Mode DEFAULT for DMA_CHREQMASKC */
#define DMA_CHREQMASKC_CH4REQMASKC_DEFAULT              (_DMA_CHREQMASKC_CH4REQMASKC_DEFAULT << 4) /**< Shifted mode DEFAULT for DMA_CHREQMASKC */
#define DMA_CHREQMASKC_CH5REQMASKC                      (0x1UL << 5)                               /**< Channel 5 Request Mask Clear */
#define _DMA_CHREQMASKC_CH5REQMASKC_SHIFT               5                                          /**< Shift value for DMA_CH5REQMASKC */
#define _DMA_CHREQMASKC_CH5REQMASKC_MASK                0x20UL                                     /**< Bit mask for DMA_CH5REQMASKC */
#define _DMA_CHREQMASKC_CH5REQMASKC_DEFAULT             0x00000000UL                               /**< Mode DEFAULT for DMA_CHREQMASKC */
#define DMA_CHREQMASKC_CH5REQMASKC_DEFAULT              (_DMA_CHREQMASKC_CH5REQMASKC_DEFAULT << 5) /**< Shifted mode DEFAULT for DMA_CHREQMASKC */
#define DMA_CHREQMASKC_CH6REQMASKC                      (0x1UL << 6)                               /**< Channel 6 Request Mask Clear */
#define _DMA_CHREQMASKC_CH6REQMASKC_SHIFT               6                                          /**< Shift value for DMA_CH6REQMASKC */
#define _DMA_CHREQMASKC_CH6REQMASKC_MASK                0x40UL                                     /**< Bit mask for DMA_CH6REQMASKC */
#define _DMA_CHREQMASKC_CH6REQMASKC_DEFAULT             0x00000000UL                               /**< Mode DEFAULT for DMA_CHREQMASKC */
#define DMA_CHREQMASKC_CH6REQMASKC_DEFAULT              (_DMA_CHREQMASKC_CH6REQMASKC_DEFAULT << 6) /**< Shifted mode DEFAULT for DMA_CHREQMASKC */
#define DMA_CHREQMASKC_CH7REQMASKC                      (0x1UL << 7)                               /**< Channel 7 Request Mask Clear */
#define _DMA_CHREQMASKC_CH7REQMASKC_SHIFT               7                                          /**< Shift value for DMA_CH7REQMASKC */
#define _DMA_CHREQMASKC_CH7REQMASKC_MASK                0x80UL                                     /**< Bit mask for DMA_CH7REQMASKC */
#define _DMA_CHREQMASKC_CH7REQMASKC_DEFAULT             0x00000000UL                               /**< Mode DEFAULT for DMA_CHREQMASKC */
#define DMA_CHREQMASKC_CH7REQMASKC_DEFAULT              (_DMA_CHREQMASKC_CH7REQMASKC_DEFAULT << 7) /**< Shifted mode DEFAULT for DMA_CHREQMASKC */

/* Bit fields for DMA CHENS */
#define _DMA_CHENS_RESETVALUE                           0x00000000UL                     /**< Default value for DMA_CHENS */
#define _DMA_CHENS_MASK                                 0x000000FFUL                     /**< Mask for DMA_CHENS */
#define DMA_CHENS_CH0ENS                                (0x1UL << 0)                     /**< Channel 0 Enable Set */
#define _DMA_CHENS_CH0ENS_SHIFT                         0                                /**< Shift value for DMA_CH0ENS */
#define _DMA_CHENS_CH0ENS_MASK                          0x1UL                            /**< Bit mask for DMA_CH0ENS */
#define _DMA_CHENS_CH0ENS_DEFAULT                       0x00000000UL                     /**< Mode DEFAULT for DMA_CHENS */
#define DMA_CHENS_CH0ENS_DEFAULT                        (_DMA_CHENS_CH0ENS_DEFAULT << 0) /**< Shifted mode DEFAULT for DMA_CHENS */
#define DMA_CHENS_CH1ENS                                (0x1UL << 1)                     /**< Channel 1 Enable Set */
#define _DMA_CHENS_CH1ENS_SHIFT                         1                                /**< Shift value for DMA_CH1ENS */
#define _DMA_CHENS_CH1ENS_MASK                          0x2UL                            /**< Bit mask for DMA_CH1ENS */
#define _DMA_CHENS_CH1ENS_DEFAULT                       0x00000000UL                     /**< Mode DEFAULT for DMA_CHENS */
#define DMA_CHENS_CH1ENS_DEFAULT                        (_DMA_CHENS_CH1ENS_DEFAULT << 1) /**< Shifted mode DEFAULT for DMA_CHENS */
#define DMA_CHENS_CH2ENS                                (0x1UL << 2)                     /**< Channel 2 Enable Set */
#define _DMA_CHENS_CH2ENS_SHIFT                         2                                /**< Shift value for DMA_CH2ENS */
#define _DMA_CHENS_CH2ENS_MASK                          0x4UL                            /**< Bit mask for DMA_CH2ENS */
#define _DMA_CHENS_CH2ENS_DEFAULT                       0x00000000UL                     /**< Mode DEFAULT for DMA_CHENS */
#define DMA_CHENS_CH2ENS_DEFAULT                        (_DMA_CHENS_CH2ENS_DEFAULT << 2) /**< Shifted mode DEFAULT for DMA_CHENS */
#define DMA_CHENS_CH3ENS                                (0x1UL << 3)                     /**< Channel 3 Enable Set */
#define _DMA_CHENS_CH3ENS_SHIFT                         3                                /**< Shift value for DMA_CH3ENS */
#define _DMA_CHENS_CH3ENS_MASK                          0x8UL                            /**< Bit mask for DMA_CH3ENS */
#define _DMA_CHENS_CH3ENS_DEFAULT                       0x00000000UL                     /**< Mode DEFAULT for DMA_CHENS */
#define DMA_CHENS_CH3ENS_DEFAULT                        (_DMA_CHENS_CH3ENS_DEFAULT << 3) /**< Shifted mode DEFAULT for DMA_CHENS */
#define DMA_CHENS_CH4ENS                                (0x1UL << 4)                     /**< Channel 4 Enable Set */
#define _DMA_CHENS_CH4ENS_SHIFT                         4                                /**< Shift value for DMA_CH4ENS */
#define _DMA_CHENS_CH4ENS_MASK                          0x10UL                           /**< Bit mask for DMA_CH4ENS */
#define _DMA_CHENS_CH4ENS_DEFAULT                       0x00000000UL                     /**< Mode DEFAULT for DMA_CHENS */
#define DMA_CHENS_CH4ENS_DEFAULT                        (_DMA_CHENS_CH4ENS_DEFAULT << 4) /**< Shifted mode DEFAULT for DMA_CHENS */
#define DMA_CHENS_CH5ENS                                (0x1UL << 5)                     /**< Channel 5 Enable Set */
#define _DMA_CHENS_CH5ENS_SHIFT                         5                                /**< Shift value for DMA_CH5ENS */
#define _DMA_CHENS_CH5ENS_MASK                          0x20UL                           /**< Bit mask for DMA_CH5ENS */
#define _DMA_CHENS_CH5ENS_DEFAULT                       0x00000000UL                     /**< Mode DEFAULT for DMA_CHENS */
#define DMA_CHENS_CH5ENS_DEFAULT                        (_DMA_CHENS_CH5ENS_DEFAULT << 5) /**< Shifted mode DEFAULT for DMA_CHENS */
#define DMA_CHENS_CH6ENS                                (0x1UL << 6)                     /**< Channel 6 Enable Set */
#define _DMA_CHENS_CH6ENS_SHIFT                         6                                /**< Shift value for DMA_CH6ENS */
#define _DMA_CHENS_CH6ENS_MASK                          0x40UL                           /**< Bit mask for DMA_CH6ENS */
#define _DMA_CHENS_CH6ENS_DEFAULT                       0x00000000UL                     /**< Mode DEFAULT for DMA_CHENS */
#define DMA_CHENS_CH6ENS_DEFAULT                        (_DMA_CHENS_CH6ENS_DEFAULT << 6) /**< Shifted mode DEFAULT for DMA_CHENS */
#define DMA_CHENS_CH7ENS                                (0x1UL << 7)                     /**< Channel 7 Enable Set */
#define _DMA_CHENS_CH7ENS_SHIFT                         7                                /**< Shift value for DMA_CH7ENS */
#define _DMA_CHENS_CH7ENS_MASK                          0x80UL                           /**< Bit mask for DMA_CH7ENS */
#define _DMA_CHENS_CH7ENS_DEFAULT                       0x00000000UL                     /**< Mode DEFAULT for DMA_CHENS */
#define DMA_CHENS_CH7ENS_DEFAULT                        (_DMA_CHENS_CH7ENS_DEFAULT << 7) /**< Shifted mode DEFAULT for DMA_CHENS */

/* Bit fields for DMA CHENC */
#define _DMA_CHENC_RESETVALUE                           0x00000000UL                     /**< Default value for DMA_CHENC */
#define _DMA_CHENC_MASK                                 0x000000FFUL                     /**< Mask for DMA_CHENC */
#define DMA_CHENC_CH0ENC                                (0x1UL << 0)                     /**< Channel 0 Enable Clear */
#define _DMA_CHENC_CH0ENC_SHIFT                         0                                /**< Shift value for DMA_CH0ENC */
#define _DMA_CHENC_CH0ENC_MASK                          0x1UL                            /**< Bit mask for DMA_CH0ENC */
#define _DMA_CHENC_CH0ENC_DEFAULT                       0x00000000UL                     /**< Mode DEFAULT for DMA_CHENC */
#define DMA_CHENC_CH0ENC_DEFAULT                        (_DMA_CHENC_CH0ENC_DEFAULT << 0) /**< Shifted mode DEFAULT for DMA_CHENC */
#define DMA_CHENC_CH1ENC                                (0x1UL << 1)                     /**< Channel 1 Enable Clear */
#define _DMA_CHENC_CH1ENC_SHIFT                         1                                /**< Shift value for DMA_CH1ENC */
#define _DMA_CHENC_CH1ENC_MASK                          0x2UL                            /**< Bit mask for DMA_CH1ENC */
#define _DMA_CHENC_CH1ENC_DEFAULT                       0x00000000UL                     /**< Mode DEFAULT for DMA_CHENC */
#define DMA_CHENC_CH1ENC_DEFAULT                        (_DMA_CHENC_CH1ENC_DEFAULT << 1) /**< Shifted mode DEFAULT for DMA_CHENC */
#define DMA_CHENC_CH2ENC                                (0x1UL << 2)                     /**< Channel 2 Enable Clear */
#define _DMA_CHENC_CH2ENC_SHIFT                         2                                /**< Shift value for DMA_CH2ENC */
#define _DMA_CHENC_CH2ENC_MASK                          0x4UL                            /**< Bit mask for DMA_CH2ENC */
#define _DMA_CHENC_CH2ENC_DEFAULT                       0x00000000UL                     /**< Mode DEFAULT for DMA_CHENC */
#define DMA_CHENC_CH2ENC_DEFAULT                        (_DMA_CHENC_CH2ENC_DEFAULT << 2) /**< Shifted mode DEFAULT for DMA_CHENC */
#define DMA_CHENC_CH3ENC                                (0x1UL << 3)                     /**< Channel 3 Enable Clear */
#define _DMA_CHENC_CH3ENC_SHIFT                         3                                /**< Shift value for DMA_CH3ENC */
#define _DMA_CHENC_CH3ENC_MASK                          0x8UL                            /**< Bit mask for DMA_CH3ENC */
#define _DMA_CHENC_CH3ENC_DEFAULT                       0x00000000UL                     /**< Mode DEFAULT for DMA_CHENC */
#define DMA_CHENC_CH3ENC_DEFAULT                        (_DMA_CHENC_CH3ENC_DEFAULT << 3) /**< Shifted mode DEFAULT for DMA_CHENC */
#define DMA_CHENC_CH4ENC                                (0x1UL << 4)                     /**< Channel 4 Enable Clear */
#define _DMA_CHENC_CH4ENC_SHIFT                         4                                /**< Shift value for DMA_CH4ENC */
#define _DMA_CHENC_CH4ENC_MASK                          0x10UL                           /**< Bit mask for DMA_CH4ENC */
#define _DMA_CHENC_CH4ENC_DEFAULT                       0x00000000UL                     /**< Mode DEFAULT for DMA_CHENC */
#define DMA_CHENC_CH4ENC_DEFAULT                        (_DMA_CHENC_CH4ENC_DEFAULT << 4) /**< Shifted mode DEFAULT for DMA_CHENC */
#define DMA_CHENC_CH5ENC                                (0x1UL << 5)                     /**< Channel 5 Enable Clear */
#define _DMA_CHENC_CH5ENC_SHIFT                         5                                /**< Shift value for DMA_CH5ENC */
#define _DMA_CHENC_CH5ENC_MASK                          0x20UL                           /**< Bit mask for DMA_CH5ENC */
#define _DMA_CHENC_CH5ENC_DEFAULT                       0x00000000UL                     /**< Mode DEFAULT for DMA_CHENC */
#define DMA_CHENC_CH5ENC_DEFAULT                        (_DMA_CHENC_CH5ENC_DEFAULT << 5) /**< Shifted mode DEFAULT for DMA_CHENC */
#define DMA_CHENC_CH6ENC                                (0x1UL << 6)                     /**< Channel 6 Enable Clear */
#define _DMA_CHENC_CH6ENC_SHIFT                         6                                /**< Shift value for DMA_CH6ENC */
#define _DMA_CHENC_CH6ENC_MASK                          0x40UL                           /**< Bit mask for DMA_CH6ENC */
#define _DMA_CHENC_CH6ENC_DEFAULT                       0x00000000UL                     /**< Mode DEFAULT for DMA_CHENC */
#define DMA_CHENC_CH6ENC_DEFAULT                        (_DMA_CHENC_CH6ENC_DEFAULT << 6) /**< Shifted mode DEFAULT for DMA_CHENC */
#define DMA_CHENC_CH7ENC                                (0x1UL << 7)                     /**< Channel 7 Enable Clear */
#define _DMA_CHENC_CH7ENC_SHIFT                         7                                /**< Shift value for DMA_CH7ENC */
#define _DMA_CHENC_CH7ENC_MASK                          0x80UL                           /**< Bit mask for DMA_CH7ENC */
#define _DMA_CHENC_CH7ENC_DEFAULT                       0x00000000UL                     /**< Mode DEFAULT for DMA_CHENC */
#define DMA_CHENC_CH7ENC_DEFAULT                        (_DMA_CHENC_CH7ENC_DEFAULT << 7) /**< Shifted mode DEFAULT for DMA_CHENC */

/* Bit fields for DMA CHALTS */
#define _DMA_CHALTS_RESETVALUE                          0x00000000UL                       /**< Default value for DMA_CHALTS */
#define _DMA_CHALTS_MASK                                0x000000FFUL                       /**< Mask for DMA_CHALTS */
#define DMA_CHALTS_CH0ALTS                              (0x1UL << 0)                       /**< Channel 0 Alternate Structure Set */
#define _DMA_CHALTS_CH0ALTS_SHIFT                       0                                  /**< Shift value for DMA_CH0ALTS */
#define _DMA_CHALTS_CH0ALTS_MASK                        0x1UL                              /**< Bit mask for DMA_CH0ALTS */
#define _DMA_CHALTS_CH0ALTS_DEFAULT                     0x00000000UL                       /**< Mode DEFAULT for DMA_CHALTS */
#define DMA_CHALTS_CH0ALTS_DEFAULT                      (_DMA_CHALTS_CH0ALTS_DEFAULT << 0) /**< Shifted mode DEFAULT for DMA_CHALTS */
#define DMA_CHALTS_CH1ALTS                              (0x1UL << 1)                       /**< Channel 1 Alternate Structure Set */
#define _DMA_CHALTS_CH1ALTS_SHIFT                       1                                  /**< Shift value for DMA_CH1ALTS */
#define _DMA_CHALTS_CH1ALTS_MASK                        0x2UL                              /**< Bit mask for DMA_CH1ALTS */
#define _DMA_CHALTS_CH1ALTS_DEFAULT                     0x00000000UL                       /**< Mode DEFAULT for DMA_CHALTS */
#define DMA_CHALTS_CH1ALTS_DEFAULT                      (_DMA_CHALTS_CH1ALTS_DEFAULT << 1) /**< Shifted mode DEFAULT for DMA_CHALTS */
#define DMA_CHALTS_CH2ALTS                              (0x1UL << 2)                       /**< Channel 2 Alternate Structure Set */
#define _DMA_CHALTS_CH2ALTS_SHIFT                       2                                  /**< Shift value for DMA_CH2ALTS */
#define _DMA_CHALTS_CH2ALTS_MASK                        0x4UL                              /**< Bit mask for DMA_CH2ALTS */
#define _DMA_CHALTS_CH2ALTS_DEFAULT                     0x00000000UL                       /**< Mode DEFAULT for DMA_CHALTS */
#define DMA_CHALTS_CH2ALTS_DEFAULT                      (_DMA_CHALTS_CH2ALTS_DEFAULT << 2) /**< Shifted mode DEFAULT for DMA_CHALTS */
#define DMA_CHALTS_CH3ALTS                              (0x1UL << 3)                       /**< Channel 3 Alternate Structure Set */
#define _DMA_CHALTS_CH3ALTS_SHIFT                       3                                  /**< Shift value for DMA_CH3ALTS */
#define _DMA_CHALTS_CH3ALTS_MASK                        0x8UL                              /**< Bit mask for DMA_CH3ALTS */
#define _DMA_CHALTS_CH3ALTS_DEFAULT                     0x00000000UL                       /**< Mode DEFAULT for DMA_CHALTS */
#define DMA_CHALTS_CH3ALTS_DEFAULT                      (_DMA_CHALTS_CH3ALTS_DEFAULT << 3) /**< Shifted mode DEFAULT for DMA_CHALTS */
#define DMA_CHALTS_CH4ALTS                              (0x1UL << 4)                       /**< Channel 4 Alternate Structure Set */
#define _DMA_CHALTS_CH4ALTS_SHIFT                       4                                  /**< Shift value for DMA_CH4ALTS */
#define _DMA_CHALTS_CH4ALTS_MASK                        0x10UL                             /**< Bit mask for DMA_CH4ALTS */
#define _DMA_CHALTS_CH4ALTS_DEFAULT                     0x00000000UL                       /**< Mode DEFAULT for DMA_CHALTS */
#define DMA_CHALTS_CH4ALTS_DEFAULT                      (_DMA_CHALTS_CH4ALTS_DEFAULT << 4) /**< Shifted mode DEFAULT for DMA_CHALTS */
#define DMA_CHALTS_CH5ALTS                              (0x1UL << 5)                       /**< Channel 5 Alternate Structure Set */
#define _DMA_CHALTS_CH5ALTS_SHIFT                       5                                  /**< Shift value for DMA_CH5ALTS */
#define _DMA_CHALTS_CH5ALTS_MASK                        0x20UL                             /**< Bit mask for DMA_CH5ALTS */
#define _DMA_CHALTS_CH5ALTS_DEFAULT                     0x00000000UL                       /**< Mode DEFAULT for DMA_CHALTS */
#define DMA_CHALTS_CH5ALTS_DEFAULT                      (_DMA_CHALTS_CH5ALTS_DEFAULT << 5) /**< Shifted mode DEFAULT for DMA_CHALTS */
#define DMA_CHALTS_CH6ALTS                              (0x1UL << 6)                       /**< Channel 6 Alternate Structure Set */
#define _DMA_CHALTS_CH6ALTS_SHIFT                       6                                  /**< Shift value for DMA_CH6ALTS */
#define _DMA_CHALTS_CH6ALTS_MASK                        0x40UL                             /**< Bit mask for DMA_CH6ALTS */
#define _DMA_CHALTS_CH6ALTS_DEFAULT                     0x00000000UL                       /**< Mode DEFAULT for DMA_CHALTS */
#define DMA_CHALTS_CH6ALTS_DEFAULT                      (_DMA_CHALTS_CH6ALTS_DEFAULT << 6) /**< Shifted mode DEFAULT for DMA_CHALTS */
#define DMA_CHALTS_CH7ALTS                              (0x1UL << 7)                       /**< Channel 7 Alternate Structure Set */
#define _DMA_CHALTS_CH7ALTS_SHIFT                       7                                  /**< Shift value for DMA_CH7ALTS */
#define _DMA_CHALTS_CH7ALTS_MASK                        0x80UL                             /**< Bit mask for DMA_CH7ALTS */
#define _DMA_CHALTS_CH7ALTS_DEFAULT                     0x00000000UL                       /**< Mode DEFAULT for DMA_CHALTS */
#define DMA_CHALTS_CH7ALTS_DEFAULT                      (_DMA_CHALTS_CH7ALTS_DEFAULT << 7) /**< Shifted mode DEFAULT for DMA_CHALTS */

/* Bit fields for DMA CHALTC */
#define _DMA_CHALTC_RESETVALUE                          0x00000000UL                       /**< Default value for DMA_CHALTC */
#define _DMA_CHALTC_MASK                                0x000000FFUL                       /**< Mask for DMA_CHALTC */
#define DMA_CHALTC_CH0ALTC                              (0x1UL << 0)                       /**< Channel 0 Alternate Clear */
#define _DMA_CHALTC_CH0ALTC_SHIFT                       0                                  /**< Shift value for DMA_CH0ALTC */
#define _DMA_CHALTC_CH0ALTC_MASK                        0x1UL                              /**< Bit mask for DMA_CH0ALTC */
#define _DMA_CHALTC_CH0ALTC_DEFAULT                     0x00000000UL                       /**< Mode DEFAULT for DMA_CHALTC */
#define DMA_CHALTC_CH0ALTC_DEFAULT                      (_DMA_CHALTC_CH0ALTC_DEFAULT << 0) /**< Shifted mode DEFAULT for DMA_CHALTC */
#define DMA_CHALTC_CH1ALTC                              (0x1UL << 1)                       /**< Channel 1 Alternate Clear */
#define _DMA_CHALTC_CH1ALTC_SHIFT                       1                                  /**< Shift value for DMA_CH1ALTC */
#define _DMA_CHALTC_CH1ALTC_MASK                        0x2UL                              /**< Bit mask for DMA_CH1ALTC */
#define _DMA_CHALTC_CH1ALTC_DEFAULT                     0x00000000UL                       /**< Mode DEFAULT for DMA_CHALTC */
#define DMA_CHALTC_CH1ALTC_DEFAULT                      (_DMA_CHALTC_CH1ALTC_DEFAULT << 1) /**< Shifted mode DEFAULT for DMA_CHALTC */
#define DMA_CHALTC_CH2ALTC                              (0x1UL << 2)                       /**< Channel 2 Alternate Clear */
#define _DMA_CHALTC_CH2ALTC_SHIFT                       2                                  /**< Shift value for DMA_CH2ALTC */
#define _DMA_CHALTC_CH2ALTC_MASK                        0x4UL                              /**< Bit mask for DMA_CH2ALTC */
#define _DMA_CHALTC_CH2ALTC_DEFAULT                     0x00000000UL                       /**< Mode DEFAULT for DMA_CHALTC */
#define DMA_CHALTC_CH2ALTC_DEFAULT                      (_DMA_CHALTC_CH2ALTC_DEFAULT << 2) /**< Shifted mode DEFAULT for DMA_CHALTC */
#define DMA_CHALTC_CH3ALTC                              (0x1UL << 3)                       /**< Channel 3 Alternate Clear */
#define _DMA_CHALTC_CH3ALTC_SHIFT                       3                                  /**< Shift value for DMA_CH3ALTC */
#define _DMA_CHALTC_CH3ALTC_MASK                        0x8UL                              /**< Bit mask for DMA_CH3ALTC */
#define _DMA_CHALTC_CH3ALTC_DEFAULT                     0x00000000UL                       /**< Mode DEFAULT for DMA_CHALTC */
#define DMA_CHALTC_CH3ALTC_DEFAULT                      (_DMA_CHALTC_CH3ALTC_DEFAULT << 3) /**< Shifted mode DEFAULT for DMA_CHALTC */
#define DMA_CHALTC_CH4ALTC                              (0x1UL << 4)                       /**< Channel 4 Alternate Clear */
#define _DMA_CHALTC_CH4ALTC_SHIFT                       4                                  /**< Shift value for DMA_CH4ALTC */
#define _DMA_CHALTC_CH4ALTC_MASK                        0x10UL                             /**< Bit mask for DMA_CH4ALTC */
#define _DMA_CHALTC_CH4ALTC_DEFAULT                     0x00000000UL                       /**< Mode DEFAULT for DMA_CHALTC */
#define DMA_CHALTC_CH4ALTC_DEFAULT                      (_DMA_CHALTC_CH4ALTC_DEFAULT << 4) /**< Shifted mode DEFAULT for DMA_CHALTC */
#define DMA_CHALTC_CH5ALTC                              (0x1UL << 5)                       /**< Channel 5 Alternate Clear */
#define _DMA_CHALTC_CH5ALTC_SHIFT                       5                                  /**< Shift value for DMA_CH5ALTC */
#define _DMA_CHALTC_CH5ALTC_MASK                        0x20UL                             /**< Bit mask for DMA_CH5ALTC */
#define _DMA_CHALTC_CH5ALTC_DEFAULT                     0x00000000UL                       /**< Mode DEFAULT for DMA_CHALTC */
#define DMA_CHALTC_CH5ALTC_DEFAULT                      (_DMA_CHALTC_CH5ALTC_DEFAULT << 5) /**< Shifted mode DEFAULT for DMA_CHALTC */
#define DMA_CHALTC_CH6ALTC                              (0x1UL << 6)                       /**< Channel 6 Alternate Clear */
#define _DMA_CHALTC_CH6ALTC_SHIFT                       6                                  /**< Shift value for DMA_CH6ALTC */
#define _DMA_CHALTC_CH6ALTC_MASK                        0x40UL                             /**< Bit mask for DMA_CH6ALTC */
#define _DMA_CHALTC_CH6ALTC_DEFAULT                     0x00000000UL                       /**< Mode DEFAULT for DMA_CHALTC */
#define DMA_CHALTC_CH6ALTC_DEFAULT                      (_DMA_CHALTC_CH6ALTC_DEFAULT << 6) /**< Shifted mode DEFAULT for DMA_CHALTC */
#define DMA_CHALTC_CH7ALTC                              (0x1UL << 7)                       /**< Channel 7 Alternate Clear */
#define _DMA_CHALTC_CH7ALTC_SHIFT                       7                                  /**< Shift value for DMA_CH7ALTC */
#define _DMA_CHALTC_CH7ALTC_MASK                        0x80UL                             /**< Bit mask for DMA_CH7ALTC */
#define _DMA_CHALTC_CH7ALTC_DEFAULT                     0x00000000UL                       /**< Mode DEFAULT for DMA_CHALTC */
#define DMA_CHALTC_CH7ALTC_DEFAULT                      (_DMA_CHALTC_CH7ALTC_DEFAULT << 7) /**< Shifted mode DEFAULT for DMA_CHALTC */

/* Bit fields for DMA CHPRIS */
#define _DMA_CHPRIS_RESETVALUE                          0x00000000UL                       /**< Default value for DMA_CHPRIS */
#define _DMA_CHPRIS_MASK                                0x000000FFUL                       /**< Mask for DMA_CHPRIS */
#define DMA_CHPRIS_CH0PRIS                              (0x1UL << 0)                       /**< Channel 0 High Priority Set */
#define _DMA_CHPRIS_CH0PRIS_SHIFT                       0                                  /**< Shift value for DMA_CH0PRIS */
#define _DMA_CHPRIS_CH0PRIS_MASK                        0x1UL                              /**< Bit mask for DMA_CH0PRIS */
#define _DMA_CHPRIS_CH0PRIS_DEFAULT                     0x00000000UL                       /**< Mode DEFAULT for DMA_CHPRIS */
#define DMA_CHPRIS_CH0PRIS_DEFAULT                      (_DMA_CHPRIS_CH0PRIS_DEFAULT << 0) /**< Shifted mode DEFAULT for DMA_CHPRIS */
#define DMA_CHPRIS_CH1PRIS                              (0x1UL << 1)                       /**< Channel 1 High Priority Set */
#define _DMA_CHPRIS_CH1PRIS_SHIFT                       1                                  /**< Shift value for DMA_CH1PRIS */
#define _DMA_CHPRIS_CH1PRIS_MASK                        0x2UL                              /**< Bit mask for DMA_CH1PRIS */
#define _DMA_CHPRIS_CH1PRIS_DEFAULT                     0x00000000UL                       /**< Mode DEFAULT for DMA_CHPRIS */
#define DMA_CHPRIS_CH1PRIS_DEFAULT                      (_DMA_CHPRIS_CH1PRIS_DEFAULT << 1) /**< Shifted mode DEFAULT for DMA_CHPRIS */
#define DMA_CHPRIS_CH2PRIS                              (0x1UL << 2)                       /**< Channel 2 High Priority Set */
#define _DMA_CHPRIS_CH2PRIS_SHIFT                       2                                  /**< Shift value for DMA_CH2PRIS */
#define _DMA_CHPRIS_CH2PRIS_MASK                        0x4UL                              /**< Bit mask for DMA_CH2PRIS */
#define _DMA_CHPRIS_CH2PRIS_DEFAULT                     0x00000000UL                       /**< Mode DEFAULT for DMA_CHPRIS */
#define DMA_CHPRIS_CH2PRIS_DEFAULT                      (_DMA_CHPRIS_CH2PRIS_DEFAULT << 2) /**< Shifted mode DEFAULT for DMA_CHPRIS */
#define DMA_CHPRIS_CH3PRIS                              (0x1UL << 3)                       /**< Channel 3 High Priority Set */
#define _DMA_CHPRIS_CH3PRIS_SHIFT                       3                                  /**< Shift value for DMA_CH3PRIS */
#define _DMA_CHPRIS_CH3PRIS_MASK                        0x8UL                              /**< Bit mask for DMA_CH3PRIS */
#define _DMA_CHPRIS_CH3PRIS_DEFAULT                     0x00000000UL                       /**< Mode DEFAULT for DMA_CHPRIS */
#define DMA_CHPRIS_CH3PRIS_DEFAULT                      (_DMA_CHPRIS_CH3PRIS_DEFAULT << 3) /**< Shifted mode DEFAULT for DMA_CHPRIS */
#define DMA_CHPRIS_CH4PRIS                              (0x1UL << 4)                       /**< Channel 4 High Priority Set */
#define _DMA_CHPRIS_CH4PRIS_SHIFT                       4                                  /**< Shift value for DMA_CH4PRIS */
#define _DMA_CHPRIS_CH4PRIS_MASK                        0x10UL                             /**< Bit mask for DMA_CH4PRIS */
#define _DMA_CHPRIS_CH4PRIS_DEFAULT                     0x00000000UL                       /**< Mode DEFAULT for DMA_CHPRIS */
#define DMA_CHPRIS_CH4PRIS_DEFAULT                      (_DMA_CHPRIS_CH4PRIS_DEFAULT << 4) /**< Shifted mode DEFAULT for DMA_CHPRIS */
#define DMA_CHPRIS_CH5PRIS                              (0x1UL << 5)                       /**< Channel 5 High Priority Set */
#define _DMA_CHPRIS_CH5PRIS_SHIFT                       5                                  /**< Shift value for DMA_CH5PRIS */
#define _DMA_CHPRIS_CH5PRIS_MASK                        0x20UL                             /**< Bit mask for DMA_CH5PRIS */
#define _DMA_CHPRIS_CH5PRIS_DEFAULT                     0x00000000UL                       /**< Mode DEFAULT for DMA_CHPRIS */
#define DMA_CHPRIS_CH5PRIS_DEFAULT                      (_DMA_CHPRIS_CH5PRIS_DEFAULT << 5) /**< Shifted mode DEFAULT for DMA_CHPRIS */
#define DMA_CHPRIS_CH6PRIS                              (0x1UL << 6)                       /**< Channel 6 High Priority Set */
#define _DMA_CHPRIS_CH6PRIS_SHIFT                       6                                  /**< Shift value for DMA_CH6PRIS */
#define _DMA_CHPRIS_CH6PRIS_MASK                        0x40UL                             /**< Bit mask for DMA_CH6PRIS */
#define _DMA_CHPRIS_CH6PRIS_DEFAULT                     0x00000000UL                       /**< Mode DEFAULT for DMA_CHPRIS */
#define DMA_CHPRIS_CH6PRIS_DEFAULT                      (_DMA_CHPRIS_CH6PRIS_DEFAULT << 6) /**< Shifted mode DEFAULT for DMA_CHPRIS */
#define DMA_CHPRIS_CH7PRIS                              (0x1UL << 7)                       /**< Channel 7 High Priority Set */
#define _DMA_CHPRIS_CH7PRIS_SHIFT                       7                                  /**< Shift value for DMA_CH7PRIS */
#define _DMA_CHPRIS_CH7PRIS_MASK                        0x80UL                             /**< Bit mask for DMA_CH7PRIS */
#define _DMA_CHPRIS_CH7PRIS_DEFAULT                     0x00000000UL                       /**< Mode DEFAULT for DMA_CHPRIS */
#define DMA_CHPRIS_CH7PRIS_DEFAULT                      (_DMA_CHPRIS_CH7PRIS_DEFAULT << 7) /**< Shifted mode DEFAULT for DMA_CHPRIS */

/* Bit fields for DMA CHPRIC */
#define _DMA_CHPRIC_RESETVALUE                          0x00000000UL                       /**< Default value for DMA_CHPRIC */
#define _DMA_CHPRIC_MASK                                0x000000FFUL                       /**< Mask for DMA_CHPRIC */
#define DMA_CHPRIC_CH0PRIC                              (0x1UL << 0)                       /**< Channel 0 High Priority Clear */
#define _DMA_CHPRIC_CH0PRIC_SHIFT                       0                                  /**< Shift value for DMA_CH0PRIC */
#define _DMA_CHPRIC_CH0PRIC_MASK                        0x1UL                              /**< Bit mask for DMA_CH0PRIC */
#define _DMA_CHPRIC_CH0PRIC_DEFAULT                     0x00000000UL                       /**< Mode DEFAULT for DMA_CHPRIC */
#define DMA_CHPRIC_CH0PRIC_DEFAULT                      (_DMA_CHPRIC_CH0PRIC_DEFAULT << 0) /**< Shifted mode DEFAULT for DMA_CHPRIC */
#define DMA_CHPRIC_CH1PRIC                              (0x1UL << 1)                       /**< Channel 1 High Priority Clear */
#define _DMA_CHPRIC_CH1PRIC_SHIFT                       1                                  /**< Shift value for DMA_CH1PRIC */
#define _DMA_CHPRIC_CH1PRIC_MASK                        0x2UL                              /**< Bit mask for DMA_CH1PRIC */
#define _DMA_CHPRIC_CH1PRIC_DEFAULT                     0x00000000UL                       /**< Mode DEFAULT for DMA_CHPRIC */
#define DMA_CHPRIC_CH1PRIC_DEFAULT                      (_DMA_CHPRIC_CH1PRIC_DEFAULT << 1) /**< Shifted mode DEFAULT for DMA_CHPRIC */
#define DMA_CHPRIC_CH2PRIC                              (0x1UL << 2)                       /**< Channel 2 High Priority Clear */
#define _DMA_CHPRIC_CH2PRIC_SHIFT                       2                                  /**< Shift value for DMA_CH2PRIC */
#define _DMA_CHPRIC_CH2PRIC_MASK                        0x4UL                              /**< Bit mask for DMA_CH2PRIC */
#define _DMA_CHPRIC_CH2PRIC_DEFAULT                     0x00000000UL                       /**< Mode DEFAULT for DMA_CHPRIC */
#define DMA_CHPRIC_CH2PRIC_DEFAULT                      (_DMA_CHPRIC_CH2PRIC_DEFAULT << 2) /**< Shifted mode DEFAULT for DMA_CHPRIC */
#define DMA_CHPRIC_CH3PRIC                              (0x1UL << 3)                       /**< Channel 3 High Priority Clear */
#define _DMA_CHPRIC_CH3PRIC_SHIFT                       3                                  /**< Shift value for DMA_CH3PRIC */
#define _DMA_CHPRIC_CH3PRIC_MASK                        0x8UL                              /**< Bit mask for DMA_CH3PRIC */
#define _DMA_CHPRIC_CH3PRIC_DEFAULT                     0x00000000UL                       /**< Mode DEFAULT for DMA_CHPRIC */
#define DMA_CHPRIC_CH3PRIC_DEFAULT                      (_DMA_CHPRIC_CH3PRIC_DEFAULT << 3) /**< Shifted mode DEFAULT for DMA_CHPRIC */
#define DMA_CHPRIC_CH4PRIC                              (0x1UL << 4)                       /**< Channel 4 High Priority Clear */
#define _DMA_CHPRIC_CH4PRIC_SHIFT                       4                                  /**< Shift value for DMA_CH4PRIC */
#define _DMA_CHPRIC_CH4PRIC_MASK                        0x10UL                             /**< Bit mask for DMA_CH4PRIC */
#define _DMA_CHPRIC_CH4PRIC_DEFAULT                     0x00000000UL                       /**< Mode DEFAULT for DMA_CHPRIC */
#define DMA_CHPRIC_CH4PRIC_DEFAULT                      (_DMA_CHPRIC_CH4PRIC_DEFAULT << 4) /**< Shifted mode DEFAULT for DMA_CHPRIC */
#define DMA_CHPRIC_CH5PRIC                              (0x1UL << 5)                       /**< Channel 5 High Priority Clear */
#define _DMA_CHPRIC_CH5PRIC_SHIFT                       5                                  /**< Shift value for DMA_CH5PRIC */
#define _DMA_CHPRIC_CH5PRIC_MASK                        0x20UL                             /**< Bit mask for DMA_CH5PRIC */
#define _DMA_CHPRIC_CH5PRIC_DEFAULT                     0x00000000UL                       /**< Mode DEFAULT for DMA_CHPRIC */
#define DMA_CHPRIC_CH5PRIC_DEFAULT                      (_DMA_CHPRIC_CH5PRIC_DEFAULT << 5) /**< Shifted mode DEFAULT for DMA_CHPRIC */
#define DMA_CHPRIC_CH6PRIC                              (0x1UL << 6)                       /**< Channel 6 High Priority Clear */
#define _DMA_CHPRIC_CH6PRIC_SHIFT                       6                                  /**< Shift value for DMA_CH6PRIC */
#define _DMA_CHPRIC_CH6PRIC_MASK                        0x40UL                             /**< Bit mask for DMA_CH6PRIC */
#define _DMA_CHPRIC_CH6PRIC_DEFAULT                     0x00000000UL                       /**< Mode DEFAULT for DMA_CHPRIC */
#define DMA_CHPRIC_CH6PRIC_DEFAULT                      (_DMA_CHPRIC_CH6PRIC_DEFAULT << 6) /**< Shifted mode DEFAULT for DMA_CHPRIC */
#define DMA_CHPRIC_CH7PRIC                              (0x1UL << 7)                       /**< Channel 7 High Priority Clear */
#define _DMA_CHPRIC_CH7PRIC_SHIFT                       7                                  /**< Shift value for DMA_CH7PRIC */
#define _DMA_CHPRIC_CH7PRIC_MASK                        0x80UL                             /**< Bit mask for DMA_CH7PRIC */
#define _DMA_CHPRIC_CH7PRIC_DEFAULT                     0x00000000UL                       /**< Mode DEFAULT for DMA_CHPRIC */
#define DMA_CHPRIC_CH7PRIC_DEFAULT                      (_DMA_CHPRIC_CH7PRIC_DEFAULT << 7) /**< Shifted mode DEFAULT for DMA_CHPRIC */

/* Bit fields for DMA ERRORC */
#define _DMA_ERRORC_RESETVALUE                          0x00000000UL                      /**< Default value for DMA_ERRORC */
#define _DMA_ERRORC_MASK                                0x00000001UL                      /**< Mask for DMA_ERRORC */
#define DMA_ERRORC_ERRORC                               (0x1UL << 0)                      /**< Bus Error Clear */
#define _DMA_ERRORC_ERRORC_SHIFT                        0                                 /**< Shift value for DMA_ERRORC */
#define _DMA_ERRORC_ERRORC_MASK                         0x1UL                             /**< Bit mask for DMA_ERRORC */
#define _DMA_ERRORC_ERRORC_DEFAULT                      0x00000000UL                      /**< Mode DEFAULT for DMA_ERRORC */
#define DMA_ERRORC_ERRORC_DEFAULT                       (_DMA_ERRORC_ERRORC_DEFAULT << 0) /**< Shifted mode DEFAULT for DMA_ERRORC */

/* Bit fields for DMA CHREQSTATUS */
#define _DMA_CHREQSTATUS_RESETVALUE                     0x00000000UL                                 /**< Default value for DMA_CHREQSTATUS */
#define _DMA_CHREQSTATUS_MASK                           0x000000FFUL                                 /**< Mask for DMA_CHREQSTATUS */
#define DMA_CHREQSTATUS_CH0REQSTATUS                    (0x1UL << 0)                                 /**< Channel 0 Request Status */
#define _DMA_CHREQSTATUS_CH0REQSTATUS_SHIFT             0                                            /**< Shift value for DMA_CH0REQSTATUS */
#define _DMA_CHREQSTATUS_CH0REQSTATUS_MASK              0x1UL                                        /**< Bit mask for DMA_CH0REQSTATUS */
#define _DMA_CHREQSTATUS_CH0REQSTATUS_DEFAULT           0x00000000UL                                 /**< Mode DEFAULT for DMA_CHREQSTATUS */
#define DMA_CHREQSTATUS_CH0REQSTATUS_DEFAULT            (_DMA_CHREQSTATUS_CH0REQSTATUS_DEFAULT << 0) /**< Shifted mode DEFAULT for DMA_CHREQSTATUS */
#define DMA_CHREQSTATUS_CH1REQSTATUS                    (0x1UL << 1)                                 /**< Channel 1 Request Status */
#define _DMA_CHREQSTATUS_CH1REQSTATUS_SHIFT             1                                            /**< Shift value for DMA_CH1REQSTATUS */
#define _DMA_CHREQSTATUS_CH1REQSTATUS_MASK              0x2UL                                        /**< Bit mask for DMA_CH1REQSTATUS */
#define _DMA_CHREQSTATUS_CH1REQSTATUS_DEFAULT           0x00000000UL                                 /**< Mode DEFAULT for DMA_CHREQSTATUS */
#define DMA_CHREQSTATUS_CH1REQSTATUS_DEFAULT            (_DMA_CHREQSTATUS_CH1REQSTATUS_DEFAULT << 1) /**< Shifted mode DEFAULT for DMA_CHREQSTATUS */
#define DMA_CHREQSTATUS_CH2REQSTATUS                    (0x1UL << 2)                                 /**< Channel 2 Request Status */
#define _DMA_CHREQSTATUS_CH2REQSTATUS_SHIFT             2                                            /**< Shift value for DMA_CH2REQSTATUS */
#define _DMA_CHREQSTATUS_CH2REQSTATUS_MASK              0x4UL                                        /**< Bit mask for DMA_CH2REQSTATUS */
#define _DMA_CHREQSTATUS_CH2REQSTATUS_DEFAULT           0x00000000UL                                 /**< Mode DEFAULT for DMA_CHREQSTATUS */
#define DMA_CHREQSTATUS_CH2REQSTATUS_DEFAULT            (_DMA_CHREQSTATUS_CH2REQSTATUS_DEFAULT << 2) /**< Shifted mode DEFAULT for DMA_CHREQSTATUS */
#define DMA_CHREQSTATUS_CH3REQSTATUS                    (0x1UL << 3)                                 /**< Channel 3 Request Status */
#define _DMA_CHREQSTATUS_CH3REQSTATUS_SHIFT             3                                            /**< Shift value for DMA_CH3REQSTATUS */
#define _DMA_CHREQSTATUS_CH3REQSTATUS_MASK              0x8UL                                        /**< Bit mask for DMA_CH3REQSTATUS */
#define _DMA_CHREQSTATUS_CH3REQSTATUS_DEFAULT           0x00000000UL                                 /**< Mode DEFAULT for DMA_CHREQSTATUS */
#define DMA_CHREQSTATUS_CH3REQSTATUS_DEFAULT            (_DMA_CHREQSTATUS_CH3REQSTATUS_DEFAULT << 3) /**< Shifted mode DEFAULT for DMA_CHREQSTATUS */
#define DMA_CHREQSTATUS_CH4REQSTATUS                    (0x1UL << 4)                                 /**< Channel 4 Request Status */
#define _DMA_CHREQSTATUS_CH4REQSTATUS_SHIFT             4                                            /**< Shift value for DMA_CH4REQSTATUS */
#define _DMA_CHREQSTATUS_CH4REQSTATUS_MASK              0x10UL                                       /**< Bit mask for DMA_CH4REQSTATUS */
#define _DMA_CHREQSTATUS_CH4REQSTATUS_DEFAULT           0x00000000UL                                 /**< Mode DEFAULT for DMA_CHREQSTATUS */
#define DMA_CHREQSTATUS_CH4REQSTATUS_DEFAULT            (_DMA_CHREQSTATUS_CH4REQSTATUS_DEFAULT << 4) /**< Shifted mode DEFAULT for DMA_CHREQSTATUS */
#define DMA_CHREQSTATUS_CH5REQSTATUS                    (0x1UL << 5)                                 /**< Channel 5 Request Status */
#define _DMA_CHREQSTATUS_CH5REQSTATUS_SHIFT             5                                            /**< Shift value for DMA_CH5REQSTATUS */
#define _DMA_CHREQSTATUS_CH5REQSTATUS_MASK              0x20UL                                       /**< Bit mask for DMA_CH5REQSTATUS */
#define _DMA_CHREQSTATUS_CH5REQSTATUS_DEFAULT           0x00000000UL                                 /**< Mode DEFAULT for DMA_CHREQSTATUS */
#define DMA_CHREQSTATUS_CH5REQSTATUS_DEFAULT            (_DMA_CHREQSTATUS_CH5REQSTATUS_DEFAULT << 5) /**< Shifted mode DEFAULT for DMA_CHREQSTATUS */
#define DMA_CHREQSTATUS_CH6REQSTATUS                    (0x1UL << 6)                                 /**< Channel 6 Request Status */
#define _DMA_CHREQSTATUS_CH6REQSTATUS_SHIFT             6                                            /**< Shift value for DMA_CH6REQSTATUS */
#define _DMA_CHREQSTATUS_CH6REQSTATUS_MASK              0x40UL                                       /**< Bit mask for DMA_CH6REQSTATUS */
#define _DMA_CHREQSTATUS_CH6REQSTATUS_DEFAULT           0x00000000UL                                 /**< Mode DEFAULT for DMA_CHREQSTATUS */
#define DMA_CHREQSTATUS_CH6REQSTATUS_DEFAULT            (_DMA_CHREQSTATUS_CH6REQSTATUS_DEFAULT << 6) /**< Shifted mode DEFAULT for DMA_CHREQSTATUS */
#define DMA_CHREQSTATUS_CH7REQSTATUS                    (0x1UL << 7)                                 /**< Channel 7 Request Status */
#define _DMA_CHREQSTATUS_CH7REQSTATUS_SHIFT             7                                            /**< Shift value for DMA_CH7REQSTATUS */
#define _DMA_CHREQSTATUS_CH7REQSTATUS_MASK              0x80UL                                       /**< Bit mask for DMA_CH7REQSTATUS */
#define _DMA_CHREQSTATUS_CH7REQSTATUS_DEFAULT           0x00000000UL                                 /**< Mode DEFAULT for DMA_CHREQSTATUS */
#define DMA_CHREQSTATUS_CH7REQSTATUS_DEFAULT            (_DMA_CHREQSTATUS_CH7REQSTATUS_DEFAULT << 7) /**< Shifted mode DEFAULT for DMA_CHREQSTATUS */

/* Bit fields for DMA CHSREQSTATUS */
#define _DMA_CHSREQSTATUS_RESETVALUE                    0x00000000UL                                   /**< Default value for DMA_CHSREQSTATUS */
#define _DMA_CHSREQSTATUS_MASK                          0x000000FFUL                                   /**< Mask for DMA_CHSREQSTATUS */
#define DMA_CHSREQSTATUS_CH0SREQSTATUS                  (0x1UL << 0)                                   /**< Channel 0 Single Request Status */
#define _DMA_CHSREQSTATUS_CH0SREQSTATUS_SHIFT           0                                              /**< Shift value for DMA_CH0SREQSTATUS */
#define _DMA_CHSREQSTATUS_CH0SREQSTATUS_MASK            0x1UL                                          /**< Bit mask for DMA_CH0SREQSTATUS */
#define _DMA_CHSREQSTATUS_CH0SREQSTATUS_DEFAULT         0x00000000UL                                   /**< Mode DEFAULT for DMA_CHSREQSTATUS */
#define DMA_CHSREQSTATUS_CH0SREQSTATUS_DEFAULT          (_DMA_CHSREQSTATUS_CH0SREQSTATUS_DEFAULT << 0) /**< Shifted mode DEFAULT for DMA_CHSREQSTATUS */
#define DMA_CHSREQSTATUS_CH1SREQSTATUS                  (0x1UL << 1)                                   /**< Channel 1 Single Request Status */
#define _DMA_CHSREQSTATUS_CH1SREQSTATUS_SHIFT           1                                              /**< Shift value for DMA_CH1SREQSTATUS */
#define _DMA_CHSREQSTATUS_CH1SREQSTATUS_MASK            0x2UL                                          /**< Bit mask for DMA_CH1SREQSTATUS */
#define _DMA_CHSREQSTATUS_CH1SREQSTATUS_DEFAULT         0x00000000UL                                   /**< Mode DEFAULT for DMA_CHSREQSTATUS */
#define DMA_CHSREQSTATUS_CH1SREQSTATUS_DEFAULT          (_DMA_CHSREQSTATUS_CH1SREQSTATUS_DEFAULT << 1) /**< Shifted mode DEFAULT for DMA_CHSREQSTATUS */
#define DMA_CHSREQSTATUS_CH2SREQSTATUS                  (0x1UL << 2)                                   /**< Channel 2 Single Request Status */
#define _DMA_CHSREQSTATUS_CH2SREQSTATUS_SHIFT           2                                              /**< Shift value for DMA_CH2SREQSTATUS */
#define _DMA_CHSREQSTATUS_CH2SREQSTATUS_MASK            0x4UL                                          /**< Bit mask for DMA_CH2SREQSTATUS */
#define _DMA_CHSREQSTATUS_CH2SREQSTATUS_DEFAULT         0x00000000UL                                   /**< Mode DEFAULT for DMA_CHSREQSTATUS */
#define DMA_CHSREQSTATUS_CH2SREQSTATUS_DEFAULT          (_DMA_CHSREQSTATUS_CH2SREQSTATUS_DEFAULT << 2) /**< Shifted mode DEFAULT for DMA_CHSREQSTATUS */
#define DMA_CHSREQSTATUS_CH3SREQSTATUS                  (0x1UL << 3)                                   /**< Channel 3 Single Request Status */
#define _DMA_CHSREQSTATUS_CH3SREQSTATUS_SHIFT           3                                              /**< Shift value for DMA_CH3SREQSTATUS */
#define _DMA_CHSREQSTATUS_CH3SREQSTATUS_MASK            0x8UL                                          /**< Bit mask for DMA_CH3SREQSTATUS */
#define _DMA_CHSREQSTATUS_CH3SREQSTATUS_DEFAULT         0x00000000UL                                   /**< Mode DEFAULT for DMA_CHSREQSTATUS */
#define DMA_CHSREQSTATUS_CH3SREQSTATUS_DEFAULT          (_DMA_CHSREQSTATUS_CH3SREQSTATUS_DEFAULT << 3) /**< Shifted mode DEFAULT for DMA_CHSREQSTATUS */
#define DMA_CHSREQSTATUS_CH4SREQSTATUS                  (0x1UL << 4)                                   /**< Channel 4 Single Request Status */
#define _DMA_CHSREQSTATUS_CH4SREQSTATUS_SHIFT           4                                              /**< Shift value for DMA_CH4SREQSTATUS */
#define _DMA_CHSREQSTATUS_CH4SREQSTATUS_MASK            0x10UL                                         /**< Bit mask for DMA_CH4SREQSTATUS */
#define _DMA_CHSREQSTATUS_CH4SREQSTATUS_DEFAULT         0x00000000UL                                   /**< Mode DEFAULT for DMA_CHSREQSTATUS */
#define DMA_CHSREQSTATUS_CH4SREQSTATUS_DEFAULT          (_DMA_CHSREQSTATUS_CH4SREQSTATUS_DEFAULT << 4) /**< Shifted mode DEFAULT for DMA_CHSREQSTATUS */
#define DMA_CHSREQSTATUS_CH5SREQSTATUS                  (0x1UL << 5)                                   /**< Channel 5 Single Request Status */
#define _DMA_CHSREQSTATUS_CH5SREQSTATUS_SHIFT           5                                              /**< Shift value for DMA_CH5SREQSTATUS */
#define _DMA_CHSREQSTATUS_CH5SREQSTATUS_MASK            0x20UL                                         /**< Bit mask for DMA_CH5SREQSTATUS */
#define _DMA_CHSREQSTATUS_CH5SREQSTATUS_DEFAULT         0x00000000UL                                   /**< Mode DEFAULT for DMA_CHSREQSTATUS */
#define DMA_CHSREQSTATUS_CH5SREQSTATUS_DEFAULT          (_DMA_CHSREQSTATUS_CH5SREQSTATUS_DEFAULT << 5) /**< Shifted mode DEFAULT for DMA_CHSREQSTATUS */
#define DMA_CHSREQSTATUS_CH6SREQSTATUS                  (0x1UL << 6)                                   /**< Channel 6 Single Request Status */
#define _DMA_CHSREQSTATUS_CH6SREQSTATUS_SHIFT           6                                              /**< Shift value for DMA_CH6SREQSTATUS */
#define _DMA_CHSREQSTATUS_CH6SREQSTATUS_MASK            0x40UL                                         /**< Bit mask for DMA_CH6SREQSTATUS */
#define _DMA_CHSREQSTATUS_CH6SREQSTATUS_DEFAULT         0x00000000UL                                   /**< Mode DEFAULT for DMA_CHSREQSTATUS */
#define DMA_CHSREQSTATUS_CH6SREQSTATUS_DEFAULT          (_DMA_CHSREQSTATUS_CH6SREQSTATUS_DEFAULT << 6) /**< Shifted mode DEFAULT for DMA_CHSREQSTATUS */
#define DMA_CHSREQSTATUS_CH7SREQSTATUS                  (0x1UL << 7)                                   /**< Channel 7 Single Request Status */
#define _DMA_CHSREQSTATUS_CH7SREQSTATUS_SHIFT           7                                              /**< Shift value for DMA_CH7SREQSTATUS */
#define _DMA_CHSREQSTATUS_CH7SREQSTATUS_MASK            0x80UL                                         /**< Bit mask for DMA_CH7SREQSTATUS */
#define _DMA_CHSREQSTATUS_CH7SREQSTATUS_DEFAULT         0x00000000UL                                   /**< Mode DEFAULT for DMA_CHSREQSTATUS */
#define DMA_CHSREQSTATUS_CH7SREQSTATUS_DEFAULT          (_DMA_CHSREQSTATUS_CH7SREQSTATUS_DEFAULT << 7) /**< Shifted mode DEFAULT for DMA_CHSREQSTATUS */
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
