peterloes/HRD/Software/Device/EnergyMicro/EFM32G/Include/efm32g_dac.h

/**************************************************************************//**
 * @file
 * @brief efm32g_dac Register and Bit Field definitions
 * @author Energy Micro AS
 * @version 3.20.2
 ******************************************************************************
 * @section License
 * <b>(C) Copyright 2012 Energy Micro AS, http://www.energymicro.com</b>
 ******************************************************************************
 *
 * Permission is granted to anyone to use this software for any purpose,
 * including commercial applications, and to alter it and redistribute it
 * freely, subject to the following restrictions:
 *
 * 1. The origin of this software must not be misrepresented; you must not
 *    claim that you wrote the original software.
 * 2. Altered source versions must be plainly marked as such, and must not be
 *    misrepresented as being the original software.
 * 3. This notice may not be removed or altered from any source distribution.
 *
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
 * Energy Micro AS will not be liable for any consequential, incidental, or
 * special damages, or any other relief, or for any claim by any third party,
 * arising from your use of this Software.
 *
 *****************************************************************************/
/**************************************************************************//**
 * @defgroup EFM32G_DAC
 * @{
 * @brief EFM32G_DAC Register Declaration
 *****************************************************************************/
typedef struct
{
  __IO uint32_t CTRL;     /**< Control Register  */
  __I uint32_t  STATUS;   /**< Status Register  */
  __IO uint32_t CH0CTRL;  /**< Channel 0 Control Register  */
  __IO uint32_t CH1CTRL;  /**< Channel 1 Control Register  */
  __IO uint32_t IEN;      /**< Interrupt Enable Register  */
  __I uint32_t  IF;       /**< Interrupt Flag Register  */
  __IO uint32_t IFS;      /**< Interrupt Flag Set Register  */
  __IO uint32_t IFC;      /**< Interrupt Flag Clear Register  */
  __IO uint32_t CH0DATA;  /**< Channel 0 Data Register  */
  __IO uint32_t CH1DATA;  /**< Channel 1 Data Register  */
  __IO uint32_t COMBDATA; /**< Combined Data Register  */
  __IO uint32_t CAL;      /**< Calibration Register  */
  __IO uint32_t BIASPROG; /**< Bias Programming Register  */
} DAC_TypeDef;            /** @} */

/**************************************************************************//**
 * @defgroup EFM32G_DAC_BitFields
 * @{
 *****************************************************************************/

/* Bit fields for DAC CTRL */
#define _DAC_CTRL_RESETVALUE              0x00000010UL                         /**< Default value for DAC_CTRL */
#define _DAC_CTRL_MASK                    0x003703FFUL                         /**< Mask for DAC_CTRL */
#define DAC_CTRL_DIFF                     (0x1UL << 0)                         /**< Differential Mode */
#define _DAC_CTRL_DIFF_SHIFT              0                                    /**< Shift value for DAC_DIFF */
#define _DAC_CTRL_DIFF_MASK               0x1UL                                /**< Bit mask for DAC_DIFF */
#define _DAC_CTRL_DIFF_DEFAULT            0x00000000UL                         /**< Mode DEFAULT for DAC_CTRL */
#define DAC_CTRL_DIFF_DEFAULT             (_DAC_CTRL_DIFF_DEFAULT << 0)        /**< Shifted mode DEFAULT for DAC_CTRL */
#define DAC_CTRL_SINEMODE                 (0x1UL << 1)                         /**< Sine Mode */
#define _DAC_CTRL_SINEMODE_SHIFT          1                                    /**< Shift value for DAC_SINEMODE */
#define _DAC_CTRL_SINEMODE_MASK           0x2UL                                /**< Bit mask for DAC_SINEMODE */
#define _DAC_CTRL_SINEMODE_DEFAULT        0x00000000UL                         /**< Mode DEFAULT for DAC_CTRL */
#define DAC_CTRL_SINEMODE_DEFAULT         (_DAC_CTRL_SINEMODE_DEFAULT << 1)    /**< Shifted mode DEFAULT for DAC_CTRL */
#define _DAC_CTRL_CONVMODE_SHIFT          2                                    /**< Shift value for DAC_CONVMODE */
#define _DAC_CTRL_CONVMODE_MASK           0xCUL                                /**< Bit mask for DAC_CONVMODE */
#define _DAC_CTRL_CONVMODE_DEFAULT        0x00000000UL                         /**< Mode DEFAULT for DAC_CTRL */
#define _DAC_CTRL_CONVMODE_CONTINUOUS     0x00000000UL                         /**< Mode CONTINUOUS for DAC_CTRL */
#define _DAC_CTRL_CONVMODE_SAMPLEHOLD     0x00000001UL                         /**< Mode SAMPLEHOLD for DAC_CTRL */
#define _DAC_CTRL_CONVMODE_SAMPLEOFF      0x00000002UL                         /**< Mode SAMPLEOFF for DAC_CTRL */
#define DAC_CTRL_CONVMODE_DEFAULT         (_DAC_CTRL_CONVMODE_DEFAULT << 2)    /**< Shifted mode DEFAULT for DAC_CTRL */
#define DAC_CTRL_CONVMODE_CONTINUOUS      (_DAC_CTRL_CONVMODE_CONTINUOUS << 2) /**< Shifted mode CONTINUOUS for DAC_CTRL */
#define DAC_CTRL_CONVMODE_SAMPLEHOLD      (_DAC_CTRL_CONVMODE_SAMPLEHOLD << 2) /**< Shifted mode SAMPLEHOLD for DAC_CTRL */
#define DAC_CTRL_CONVMODE_SAMPLEOFF       (_DAC_CTRL_CONVMODE_SAMPLEOFF << 2)  /**< Shifted mode SAMPLEOFF for DAC_CTRL */
#define _DAC_CTRL_OUTMODE_SHIFT           4                                    /**< Shift value for DAC_OUTMODE */
#define _DAC_CTRL_OUTMODE_MASK            0x30UL                               /**< Bit mask for DAC_OUTMODE */
#define _DAC_CTRL_OUTMODE_DISABLE         0x00000000UL                         /**< Mode DISABLE for DAC_CTRL */
#define _DAC_CTRL_OUTMODE_DEFAULT         0x00000001UL                         /**< Mode DEFAULT for DAC_CTRL */
#define _DAC_CTRL_OUTMODE_PIN             0x00000001UL                         /**< Mode PIN for DAC_CTRL */
#define _DAC_CTRL_OUTMODE_ADC             0x00000002UL                         /**< Mode ADC for DAC_CTRL */
#define _DAC_CTRL_OUTMODE_PINADC          0x00000003UL                         /**< Mode PINADC for DAC_CTRL */
#define DAC_CTRL_OUTMODE_DISABLE          (_DAC_CTRL_OUTMODE_DISABLE << 4)     /**< Shifted mode DISABLE for DAC_CTRL */
#define DAC_CTRL_OUTMODE_DEFAULT          (_DAC_CTRL_OUTMODE_DEFAULT << 4)     /**< Shifted mode DEFAULT for DAC_CTRL */
#define DAC_CTRL_OUTMODE_PIN              (_DAC_CTRL_OUTMODE_PIN << 4)         /**< Shifted mode PIN for DAC_CTRL */
#define DAC_CTRL_OUTMODE_ADC              (_DAC_CTRL_OUTMODE_ADC << 4)         /**< Shifted mode ADC for DAC_CTRL */
#define DAC_CTRL_OUTMODE_PINADC           (_DAC_CTRL_OUTMODE_PINADC << 4)      /**< Shifted mode PINADC for DAC_CTRL */
#define DAC_CTRL_OUTENPRS                 (0x1UL << 6)                         /**< PRS Controlled Output Enable */
#define _DAC_CTRL_OUTENPRS_SHIFT          6                                    /**< Shift value for DAC_OUTENPRS */
#define _DAC_CTRL_OUTENPRS_MASK           0x40UL                               /**< Bit mask for DAC_OUTENPRS */
#define _DAC_CTRL_OUTENPRS_DEFAULT        0x00000000UL                         /**< Mode DEFAULT for DAC_CTRL */
#define DAC_CTRL_OUTENPRS_DEFAULT         (_DAC_CTRL_OUTENPRS_DEFAULT << 6)    /**< Shifted mode DEFAULT for DAC_CTRL */
#define DAC_CTRL_CH0PRESCRST              (0x1UL << 7)                         /**< Channel 0 Start Reset Prescaler */
#define _DAC_CTRL_CH0PRESCRST_SHIFT       7                                    /**< Shift value for DAC_CH0PRESCRST */
#define _DAC_CTRL_CH0PRESCRST_MASK        0x80UL                               /**< Bit mask for DAC_CH0PRESCRST */
#define _DAC_CTRL_CH0PRESCRST_DEFAULT     0x00000000UL                         /**< Mode DEFAULT for DAC_CTRL */
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
